phaseseeker/RotorRE/pics/front_resized.jpg

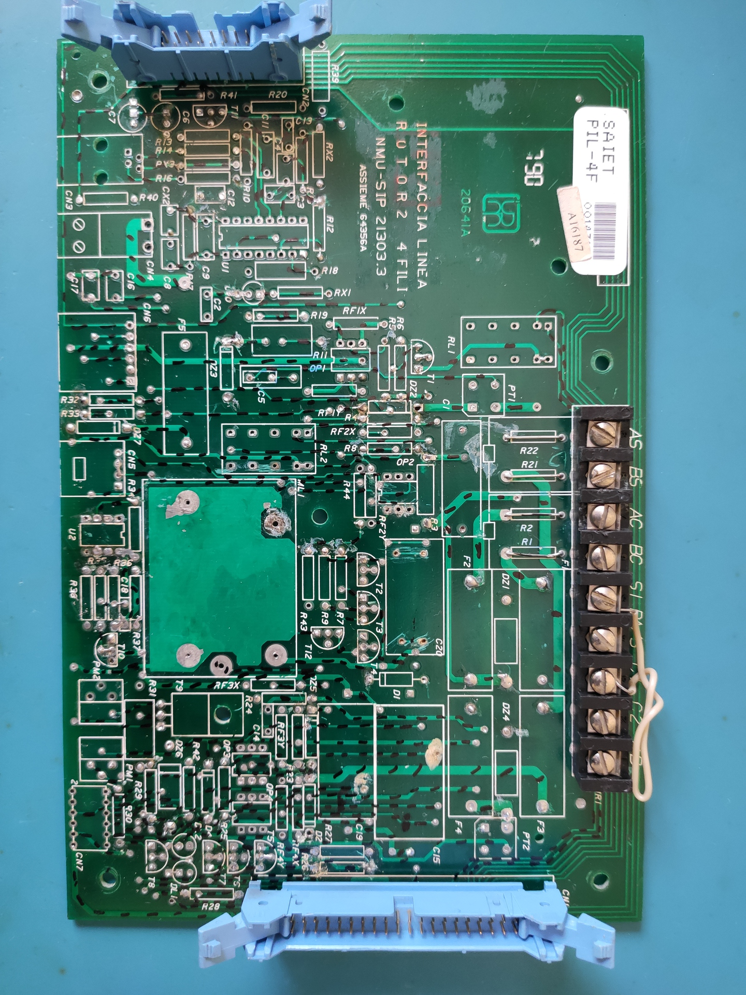
pics/front_resized.jpg
