phaseseeker/RotorRE/pics/IMG_20210405_110229_resized.jpg

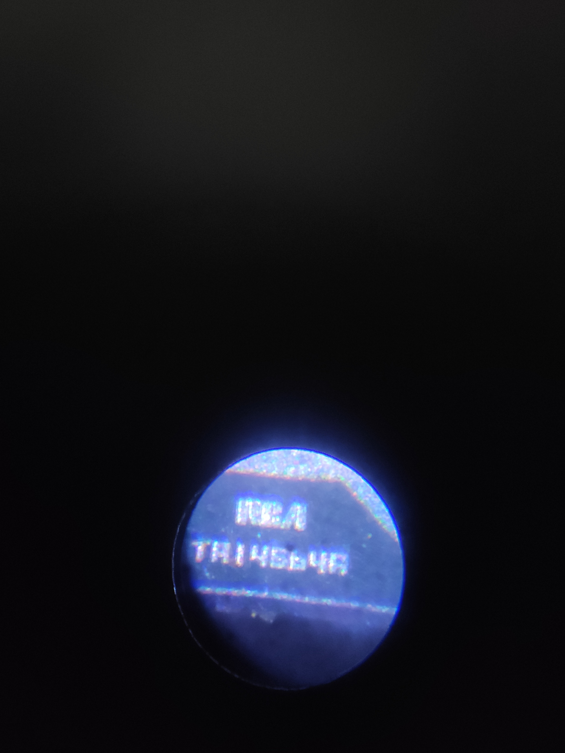
pics/IMG_20210405_110229_resized.jpg
