phaseseeker/RotorRE/pics/IMG_20210417_101937_resized.jpg

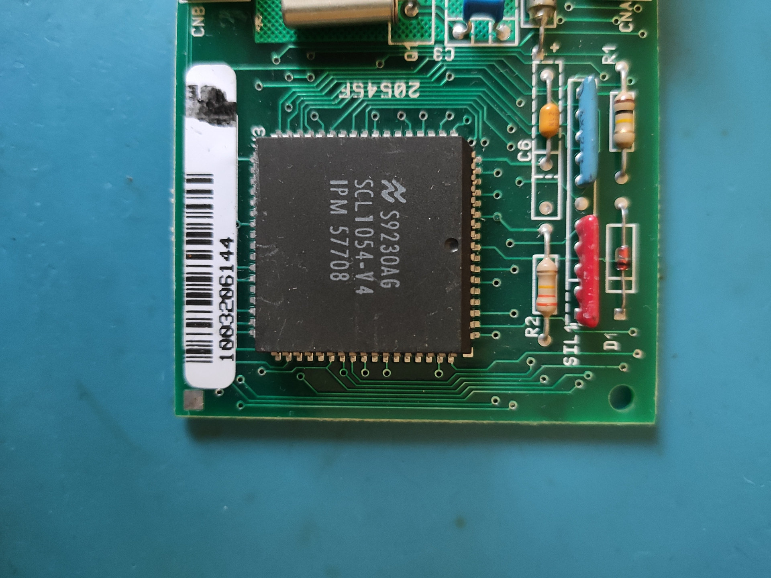
pics/IMG_20210417_101937_resized.jpg
