phaseseeker/RotorRE/pics/IMG_20210930_120020_resized.jpg

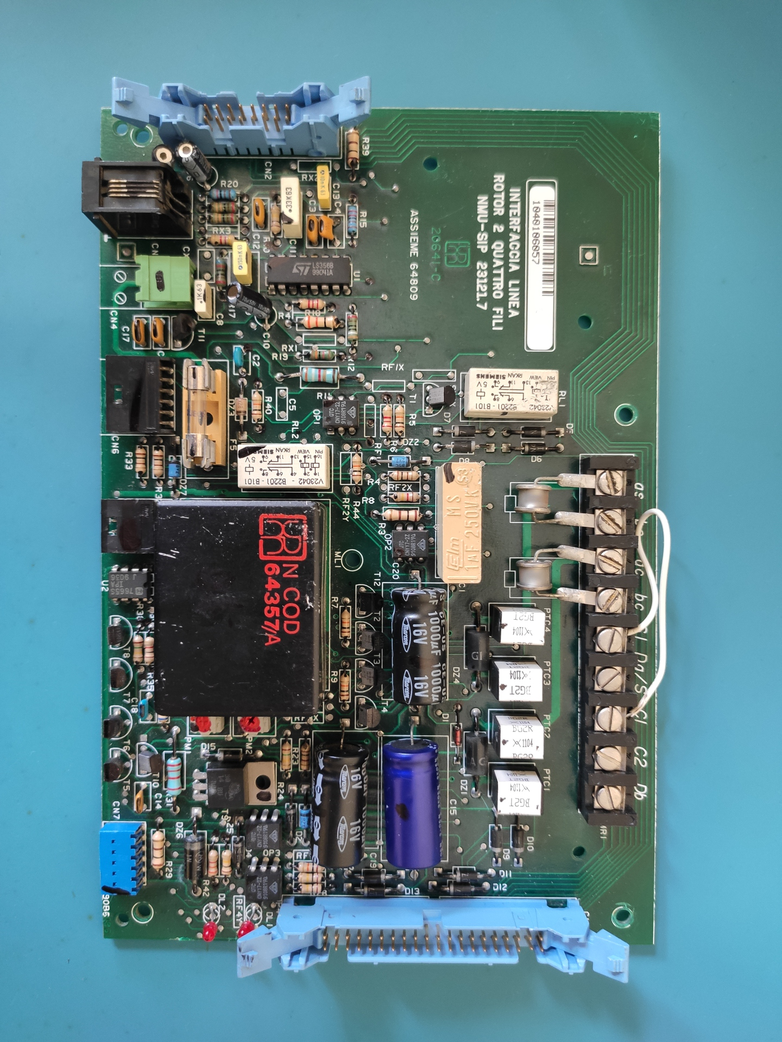
pics/IMG_20210930_120020_resized.jpg
