phaseseeker/RotorRE/pics/IMG_20210930_120023_resized.jpg

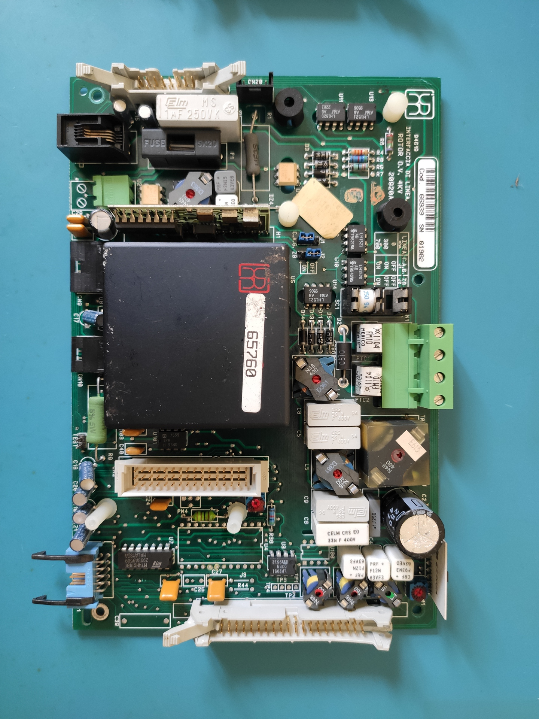
pics/IMG_20210930_120023_resized.jpg
