phaseseeker/RotorRE/pics/IMG_20210930_120042_resized.jpg

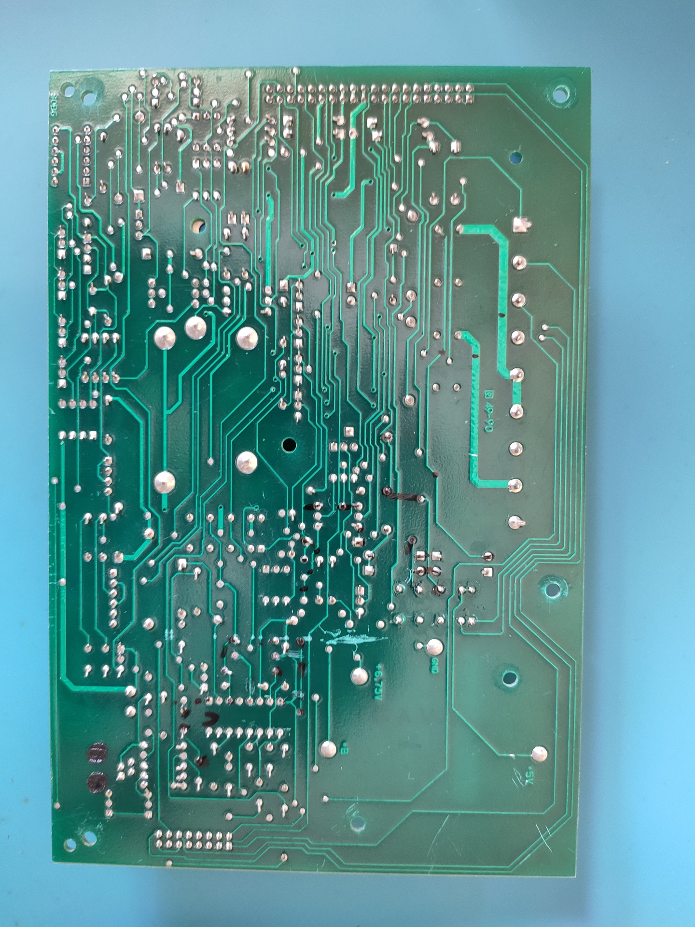
pics/IMG_20210930_120042_resized.jpg
