phaseseeker/RotorRE/pics/IMG_20210930_120044_resized.jpg

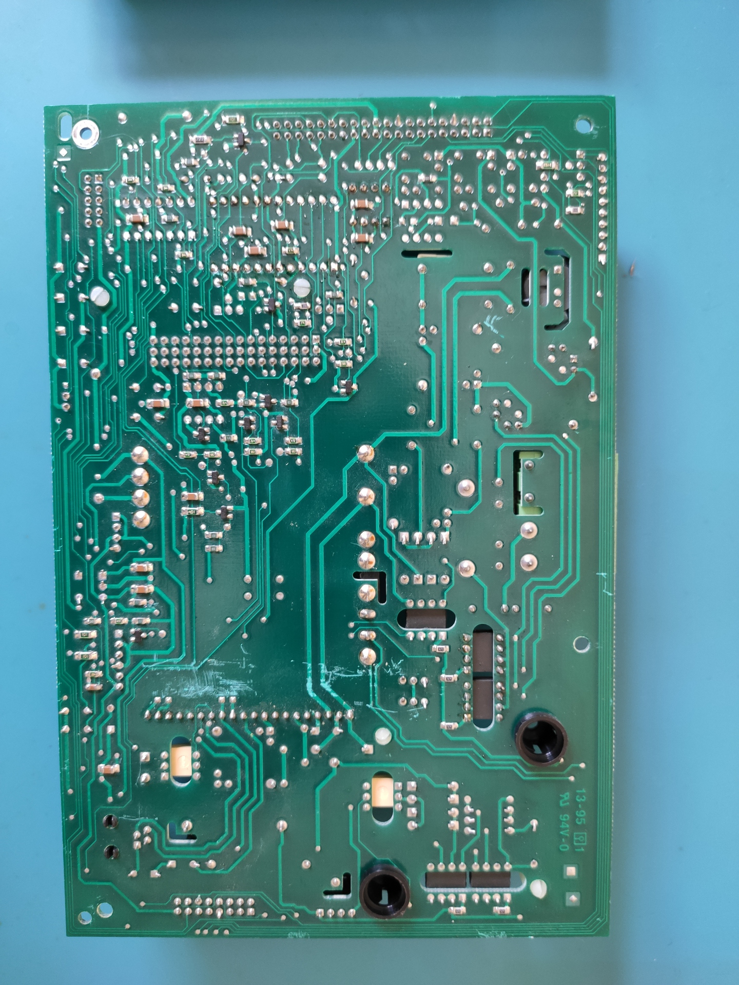
pics/IMG_20210930_120044_resized.jpg
