phaseseeker/RotorRE/pics/IMG_20210930_120053_resized.jpg

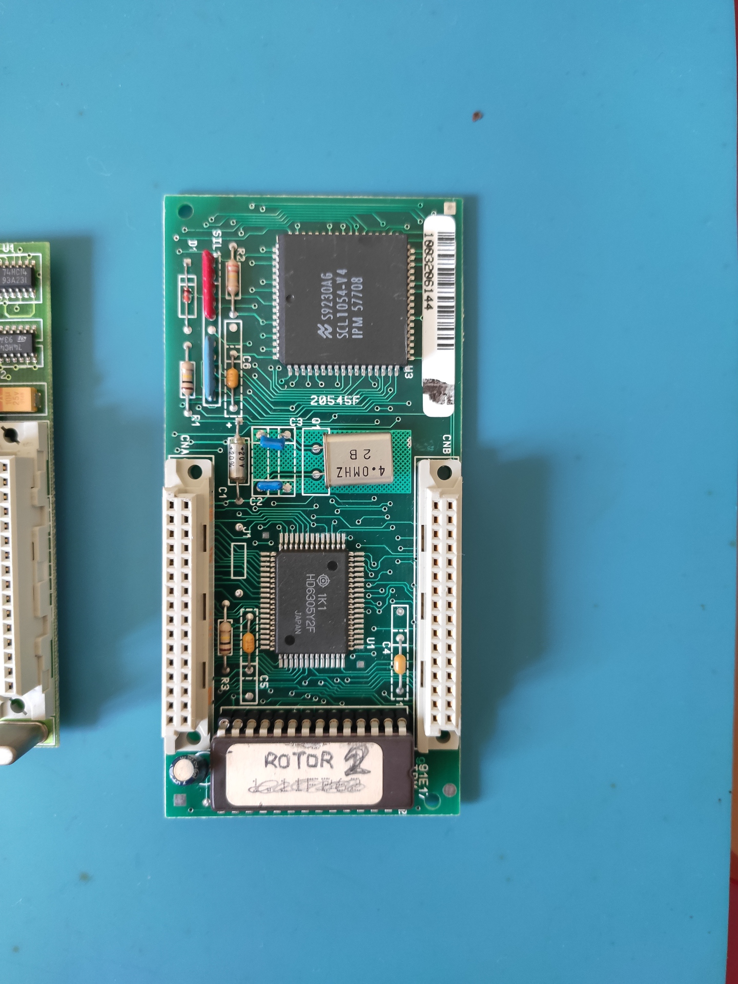
pics/IMG_20210930_120053_resized.jpg
