phaseseeker/RotorRE/pics/IMG_20210930_120104_resized.jpg

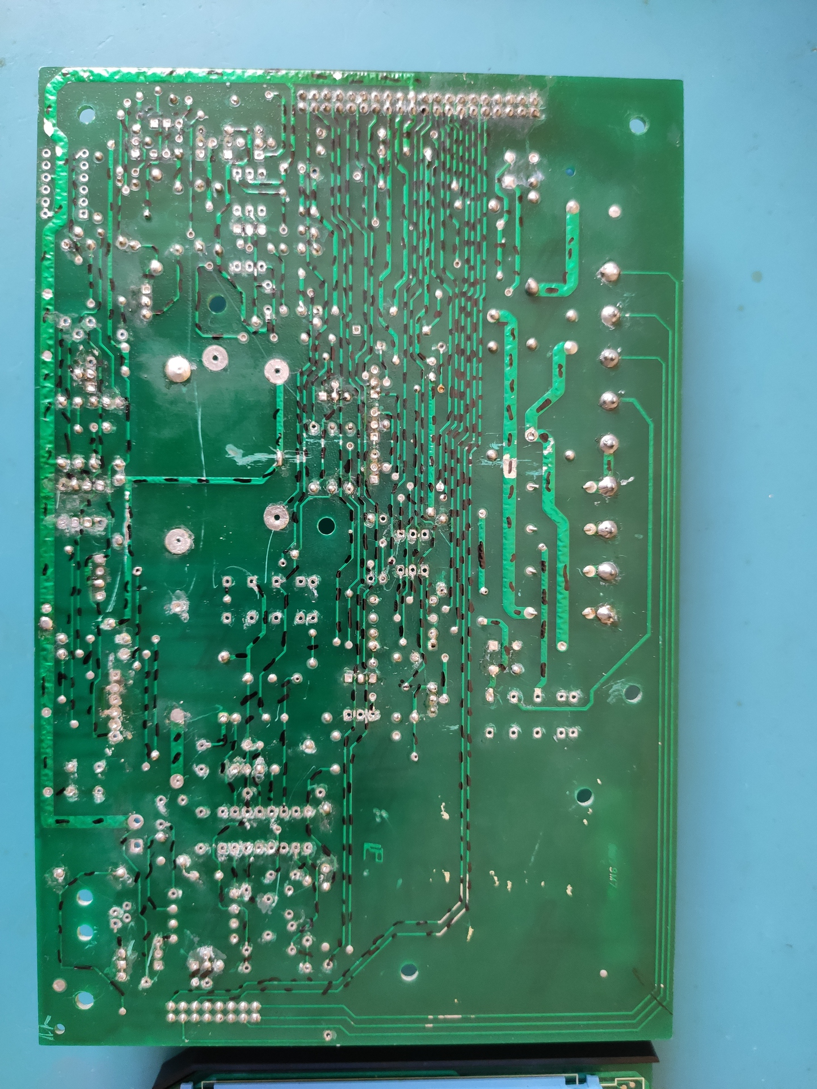
pics/IMG_20210930_120104_resized.jpg
