phaseseeker/RotorRE/pics/IMG_20210930_120108_resized.jpg

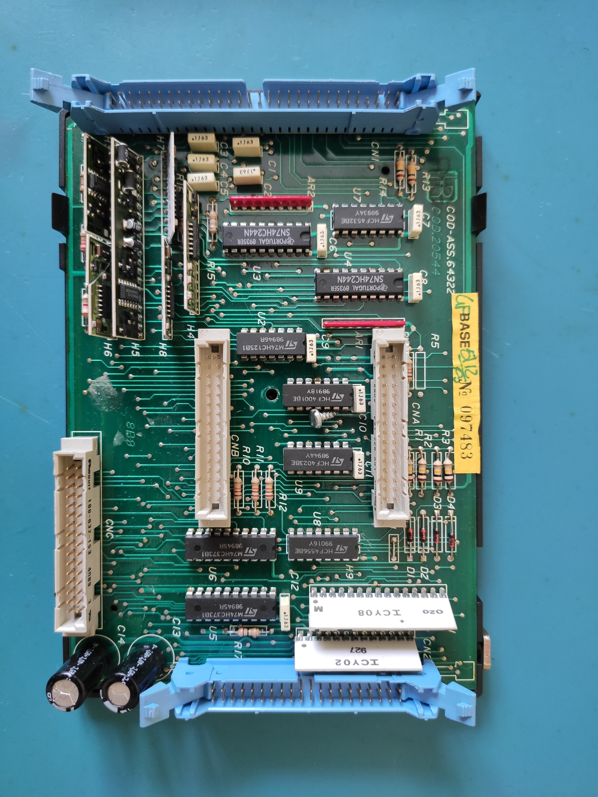
pics/IMG_20210930_120108_resized.jpg
