phaseseeker/RotorRE/pics/IMG_20210930_120112_resized.jpg

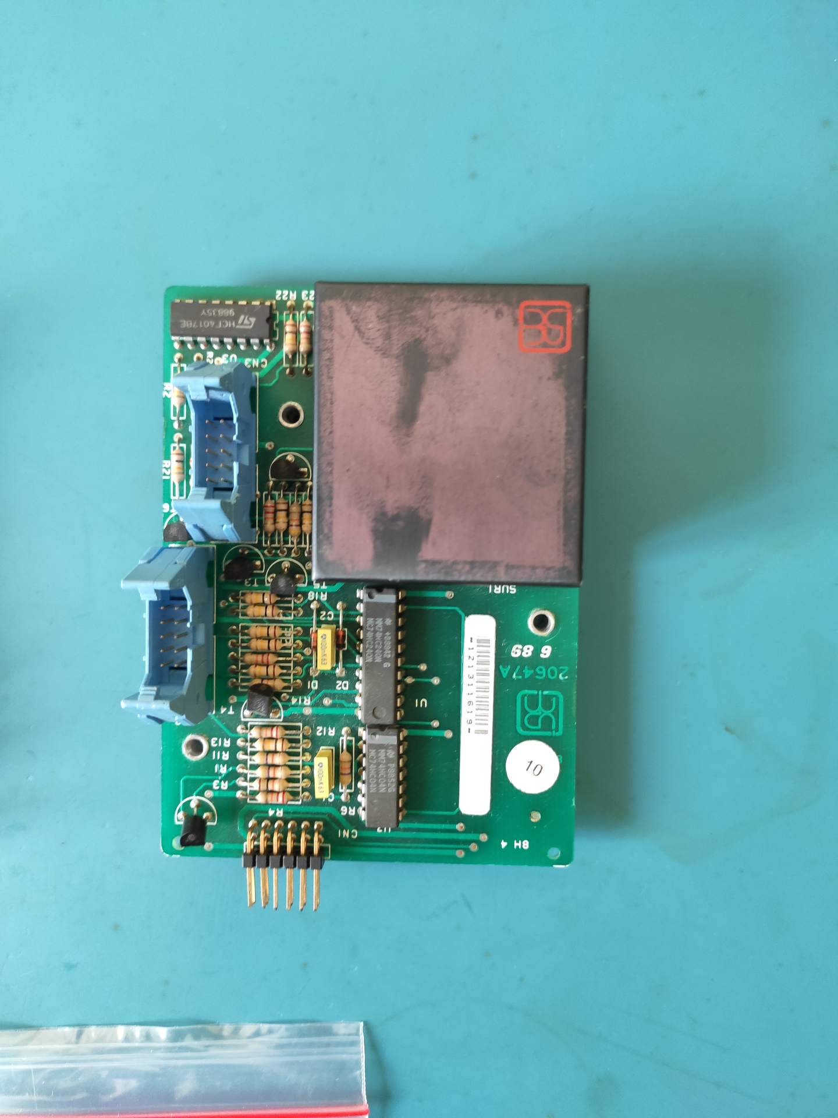
pics/IMG_20210930_120112_resized.jpg
