phaseseeker/RotorRE/pics/IMG_20210930_120115_resized.jpg

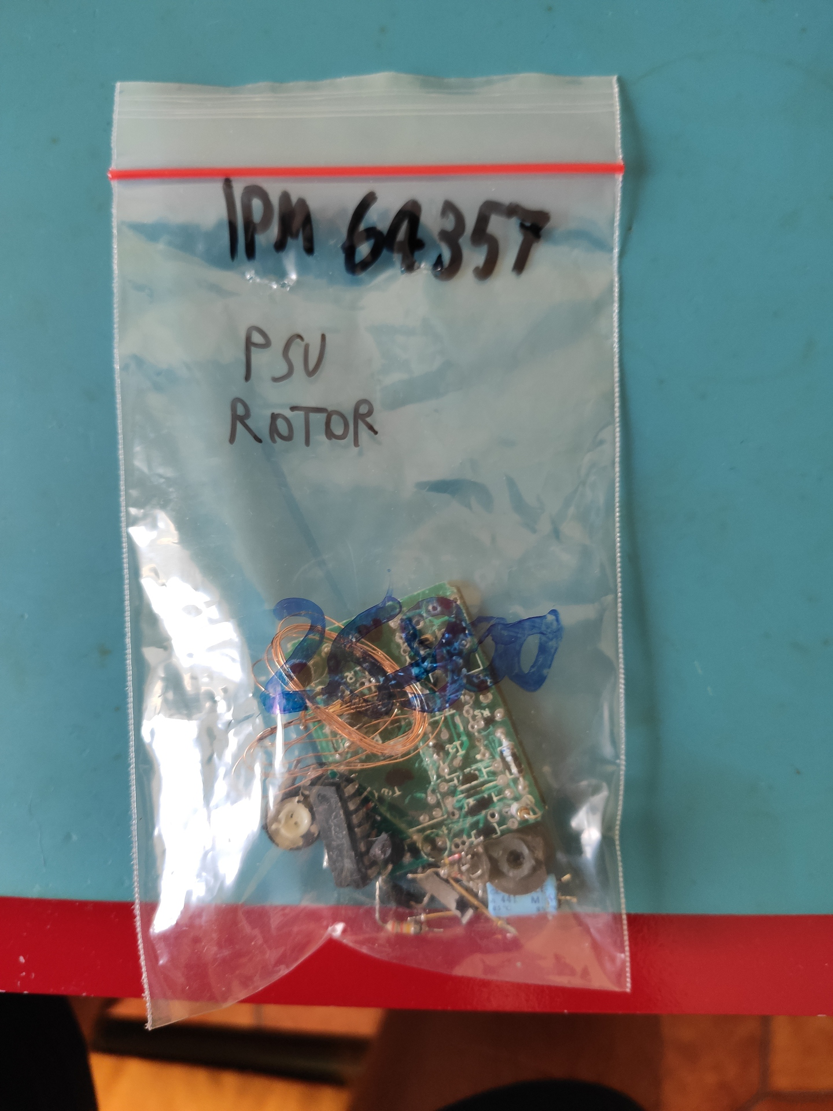
pics/IMG_20210930_120115_resized.jpg
