phaseseeker/RotorRE/pics/IMG_20210930_120138_resized.jpg

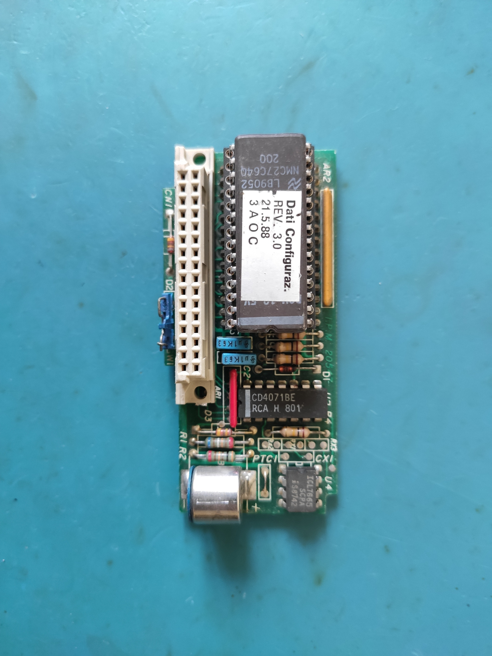
pics/IMG_20210930_120138_resized.jpg
