phaseseeker/RotorRE/pics/IMG_20210930_120150_resized.jpg

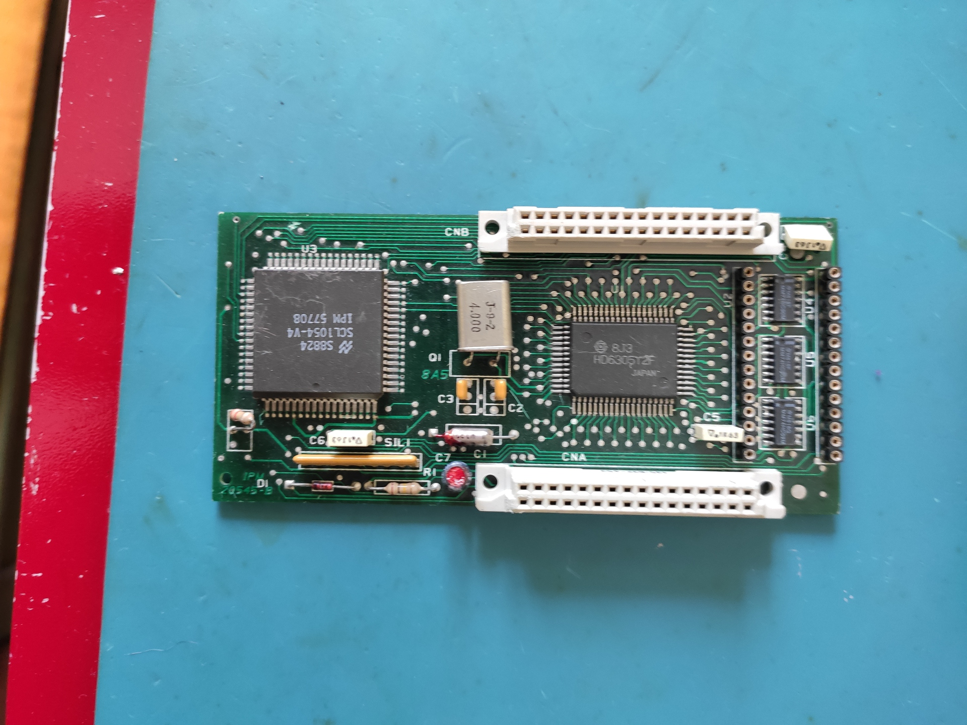
pics/IMG_20210930_120150_resized.jpg
