phaseseeker/RotorRE/pics/IMG_20210930_120319_resized.jpg

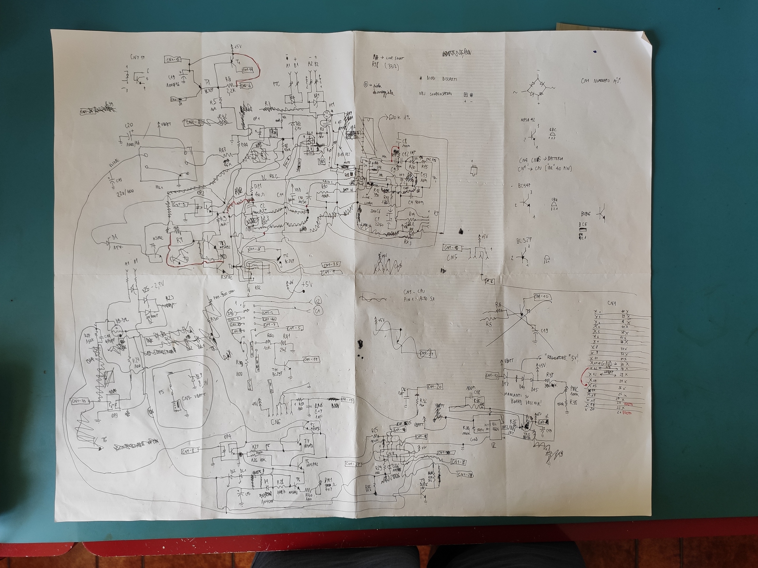
pics/IMG_20210930_120319_resized.jpg
