phaseseeker/RotorRE/pics/IMG_20210930_120355_resized.jpg

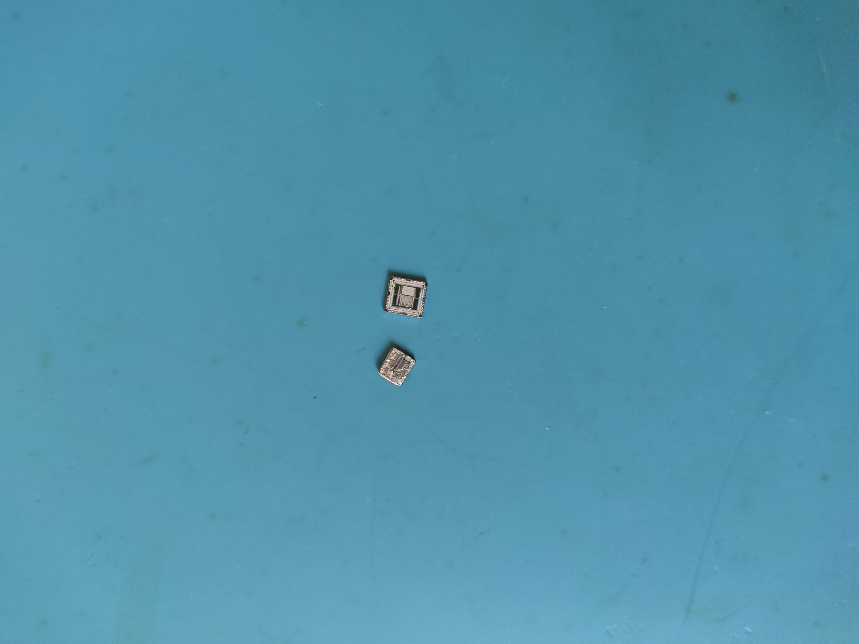
pics/IMG_20210930_120355_resized.jpg
