phaseseeker/RotorRE/pics/IMG_20210930_120400_resized.jpg

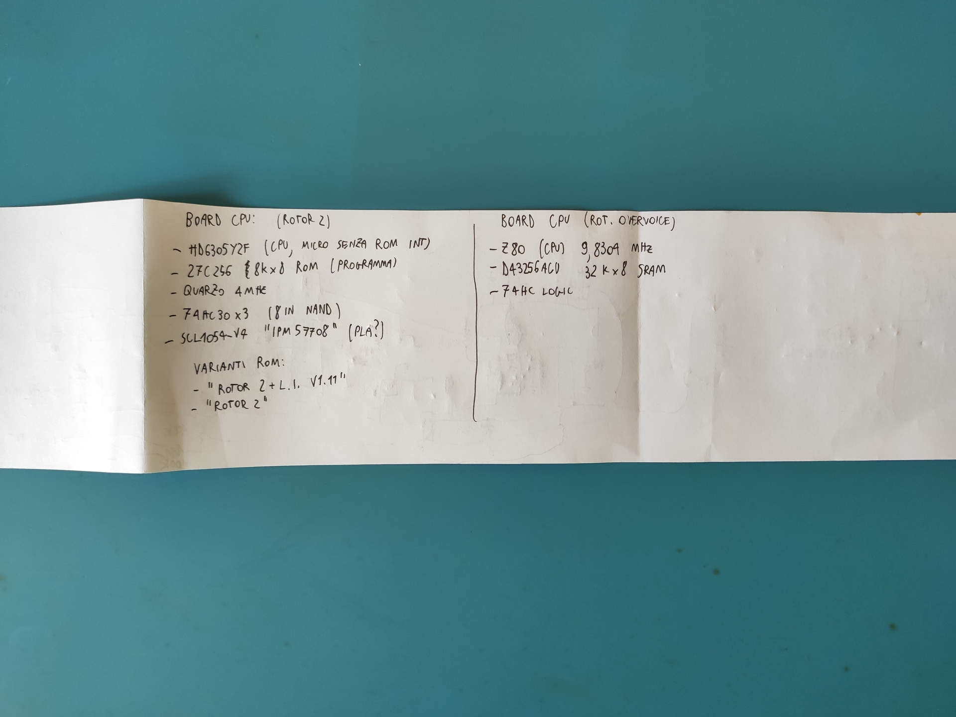
pics/IMG_20210930_120400_resized.jpg
