phaseseeker/RotorRE/pics/IMG_20210930_120421_resized.jpg

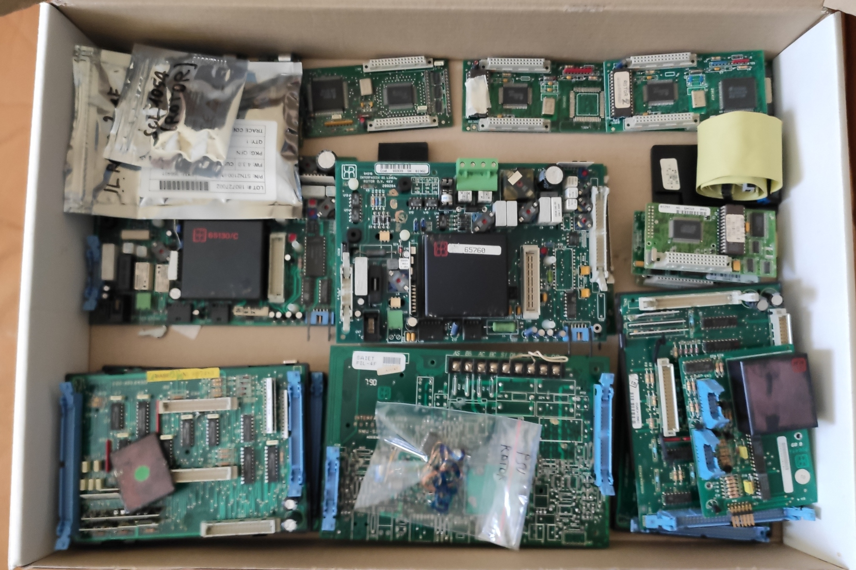
pics/IMG_20210930_120421_resized.jpg
