phaseseeker/RotorRE/pics/IMG_20210930_120958_resized.jpg

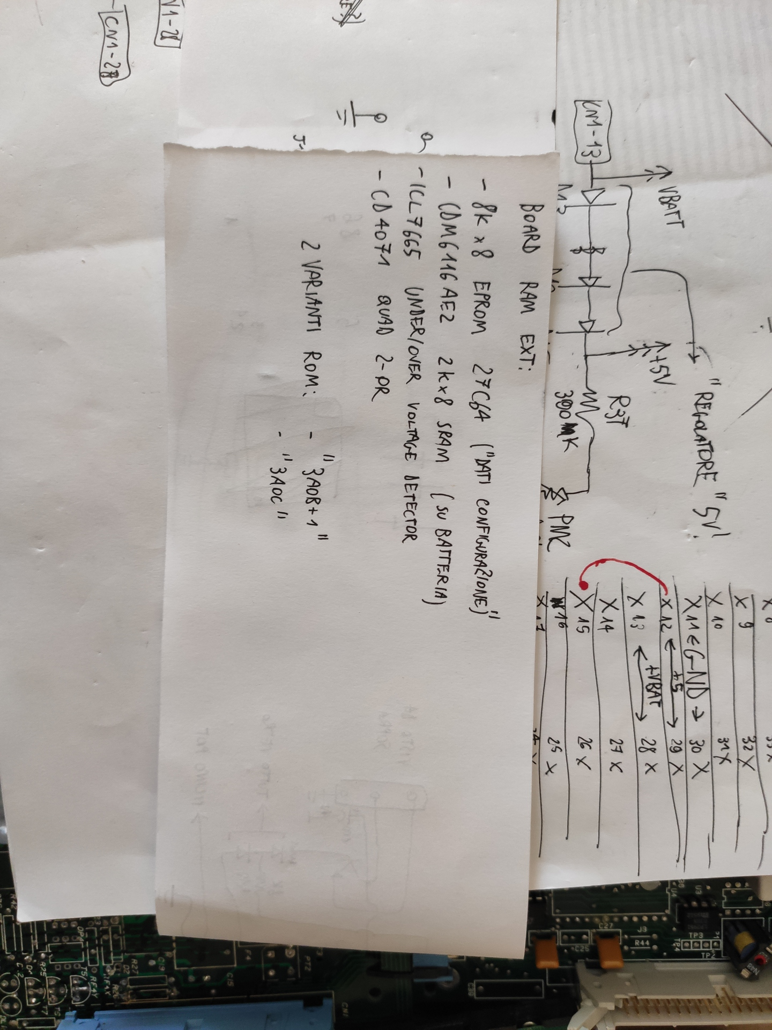
pics/IMG_20210930_120958_resized.jpg
