phaseseeker/RotorRE/pics/internals_Mech.jpg

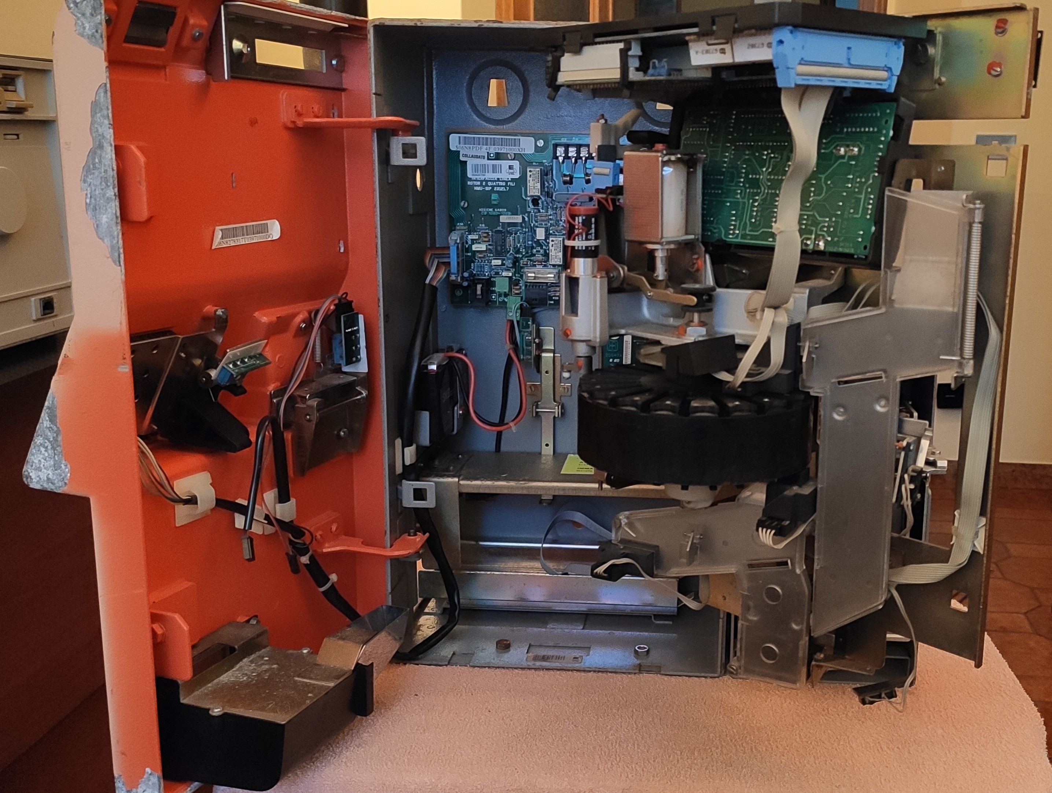
pics/internals_Mech.jpg
