phaseseeker/RotorRE/pics/internals_noMech.jpg

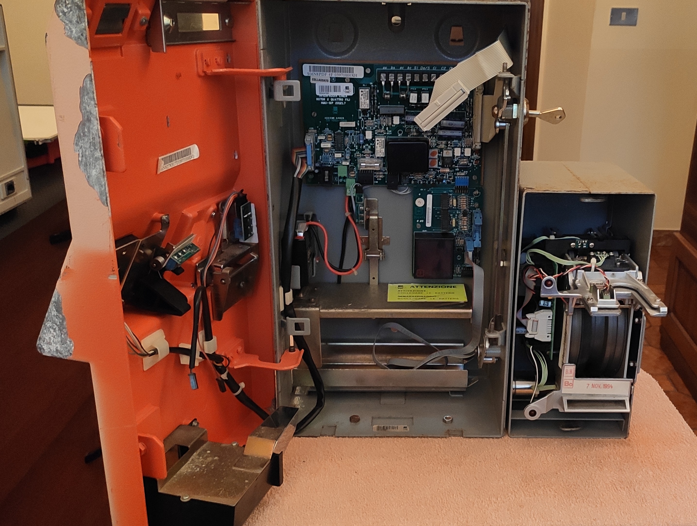
pics/internals_noMech.jpg
