phaseseeker/RotorRE/pics/liod_0_resized.jpg

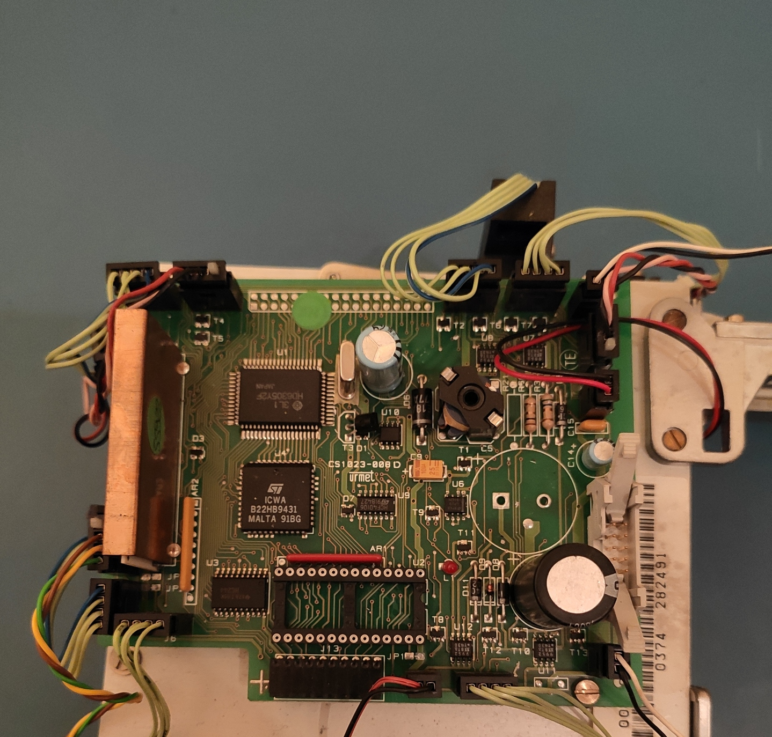
pics/liod_0_resized.jpg
