phaseseeker/RotorRE/pics/liod_1_resized.jpg

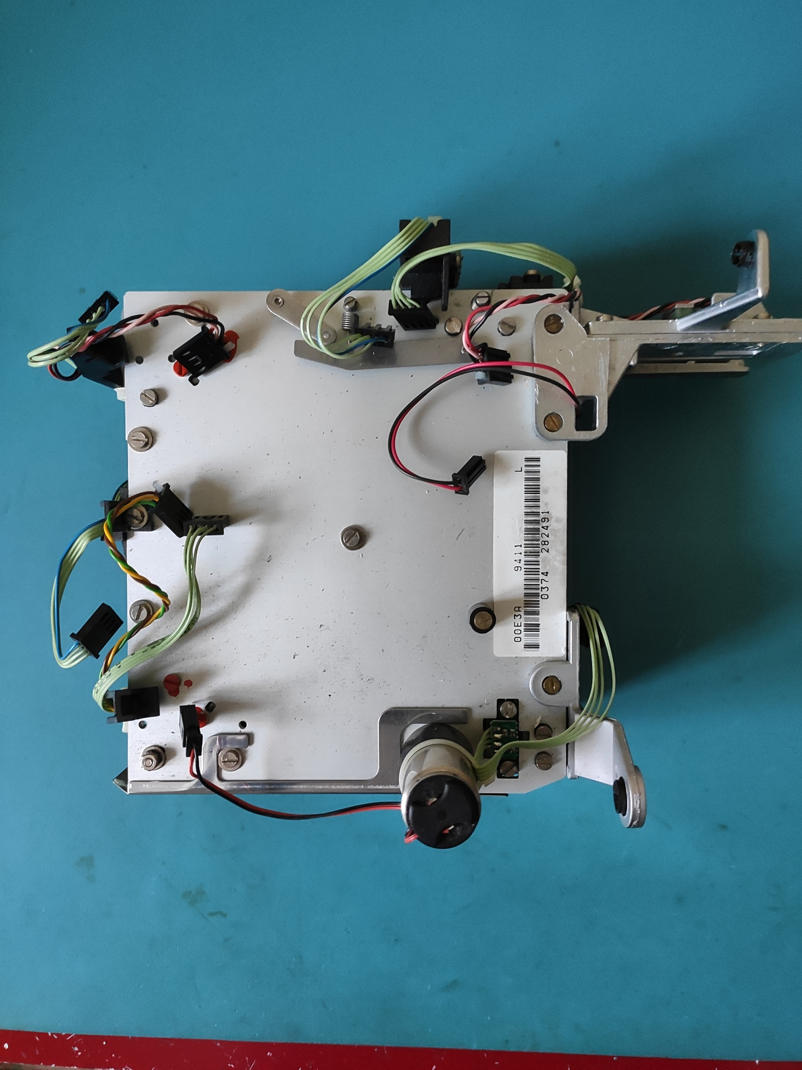
pics/liod_1_resized.jpg
