phaseseeker/RotorRE/pics/liod_2_resized.jpg

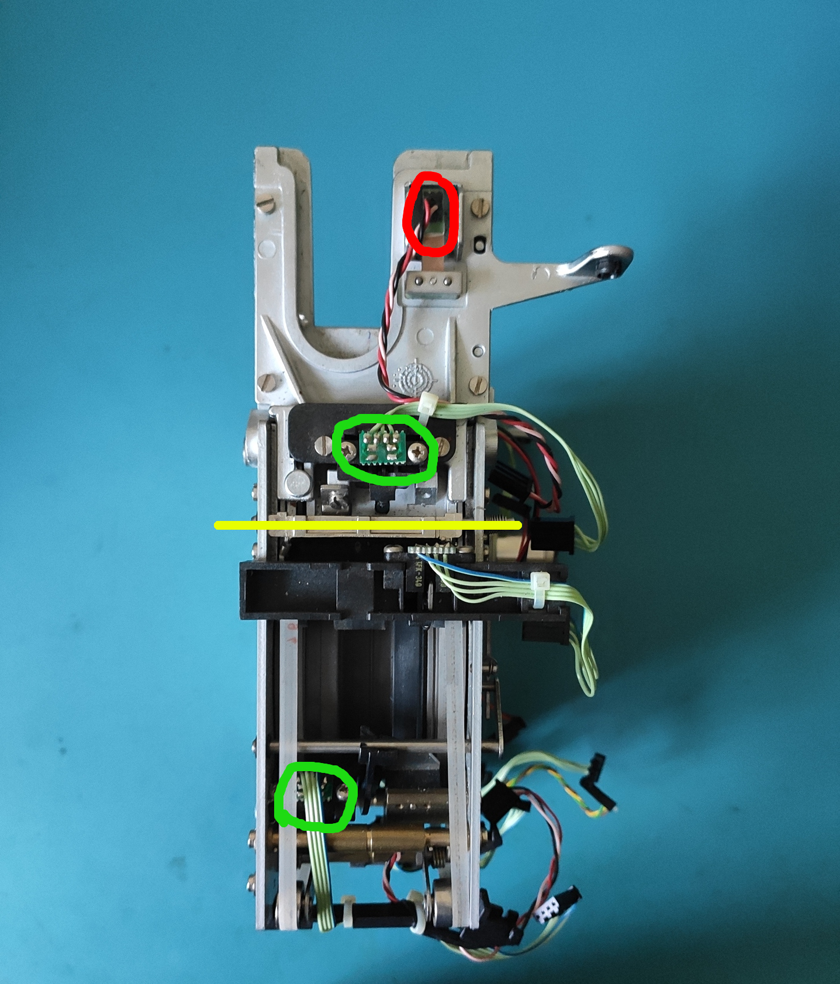
pics/liod_2_resized.jpg
