phaseseeker/RotorRE/pics/liod_3_resized.jpg

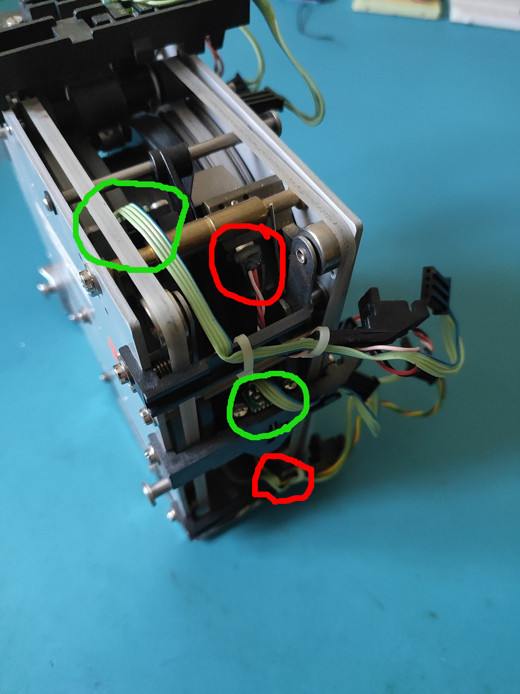
pics/liod_3_resized.jpg
