phaseseeker/RotorRE/pics/liod_4_resized.jpg

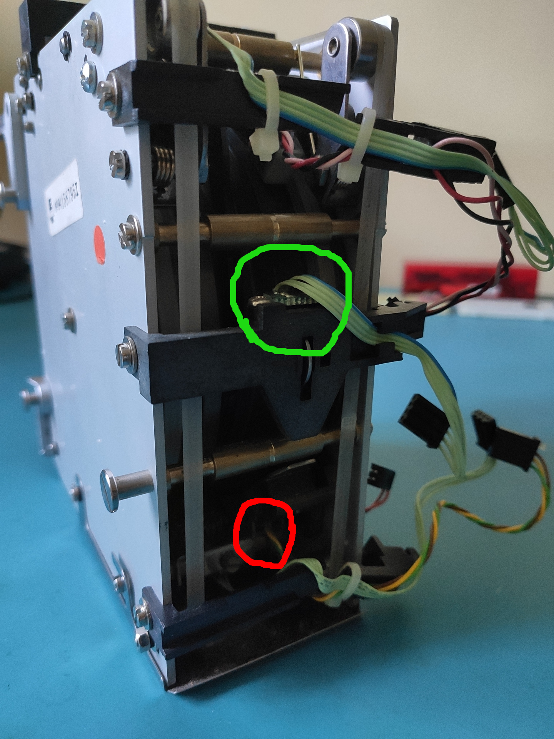
pics/liod_4_resized.jpg
