phaseseeker/RotorRE/pics/liod_5_resized.jpg

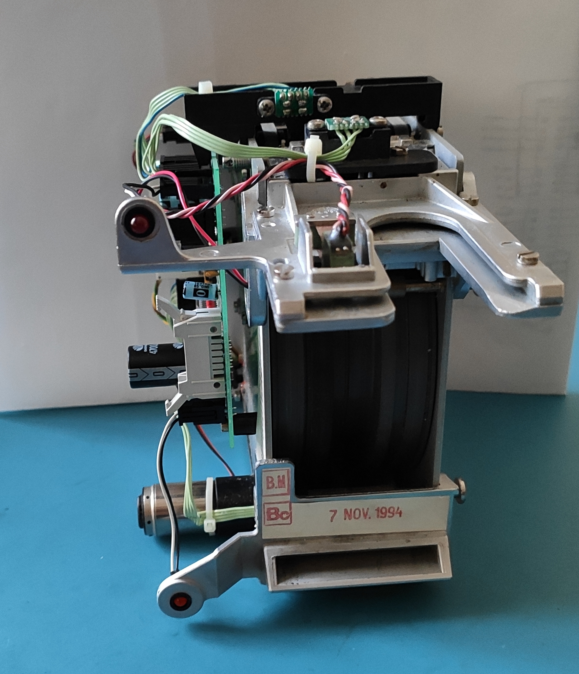
pics/liod_5_resized.jpg
