phaseseeker/RotorRE/pics/main_flippedup.jpg

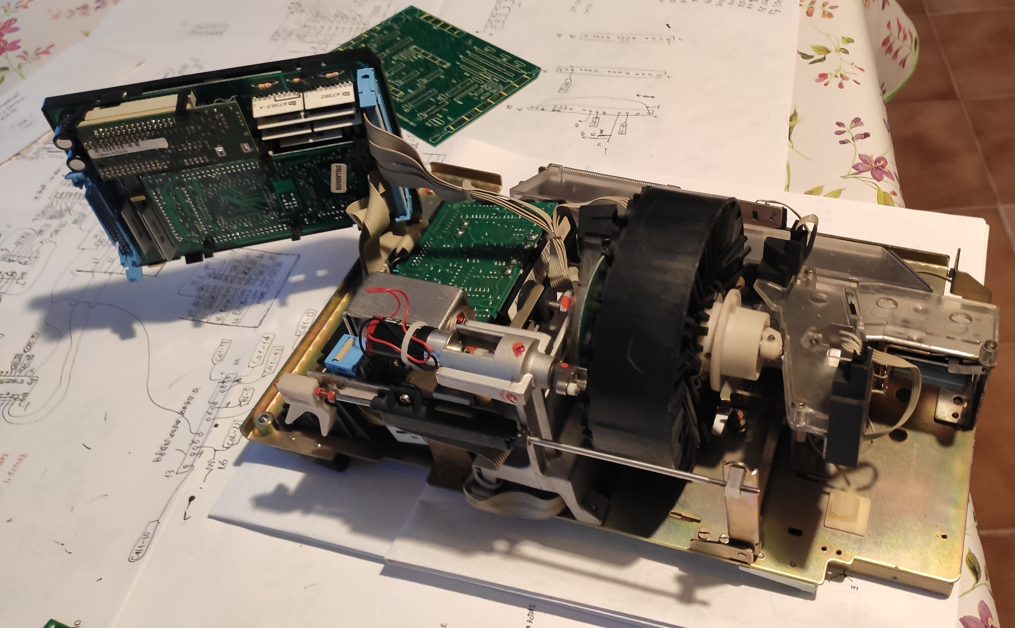
pics/main_flippedup.jpg
