phaseseeker/RotorRE/pics/main_resized.jpg

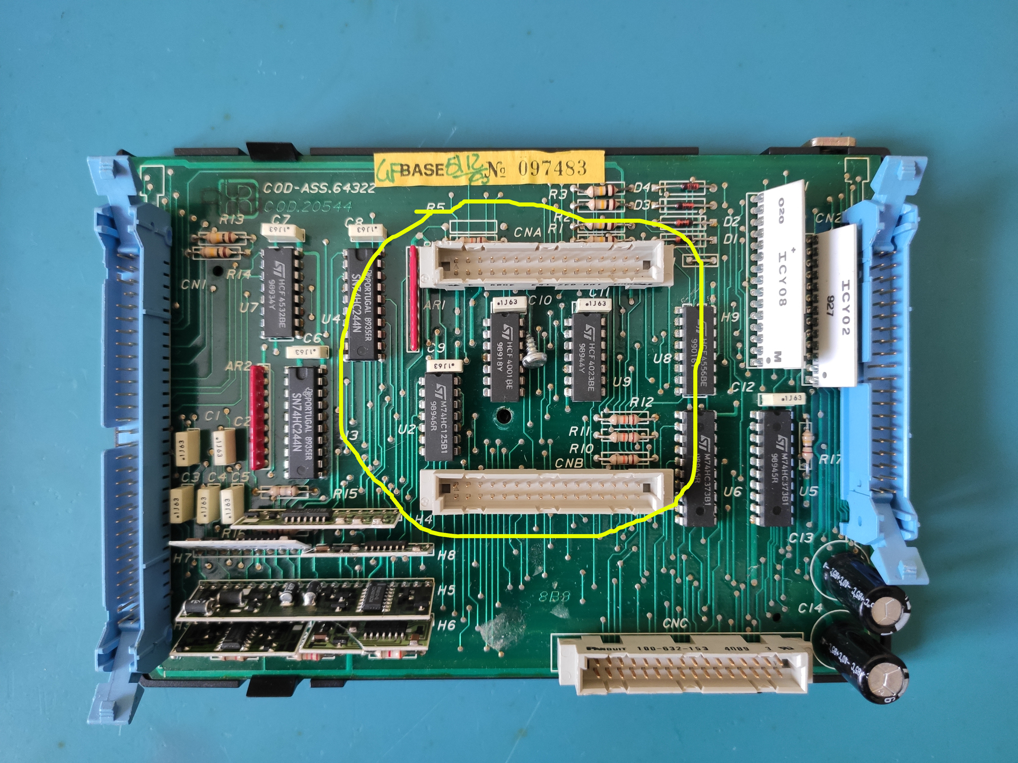
pics/main_resized.jpg
