phaseseeker/RotorRE/pics/OV_resized.jpg

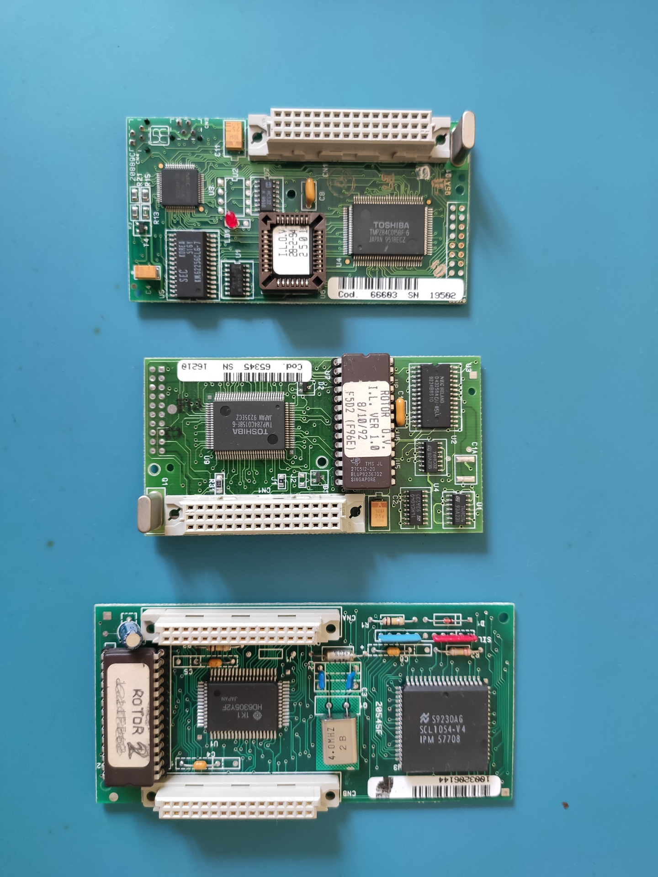
pics/OV_resized.jpg
