phaseseeker/RotorRE/pics/phone.jpeg

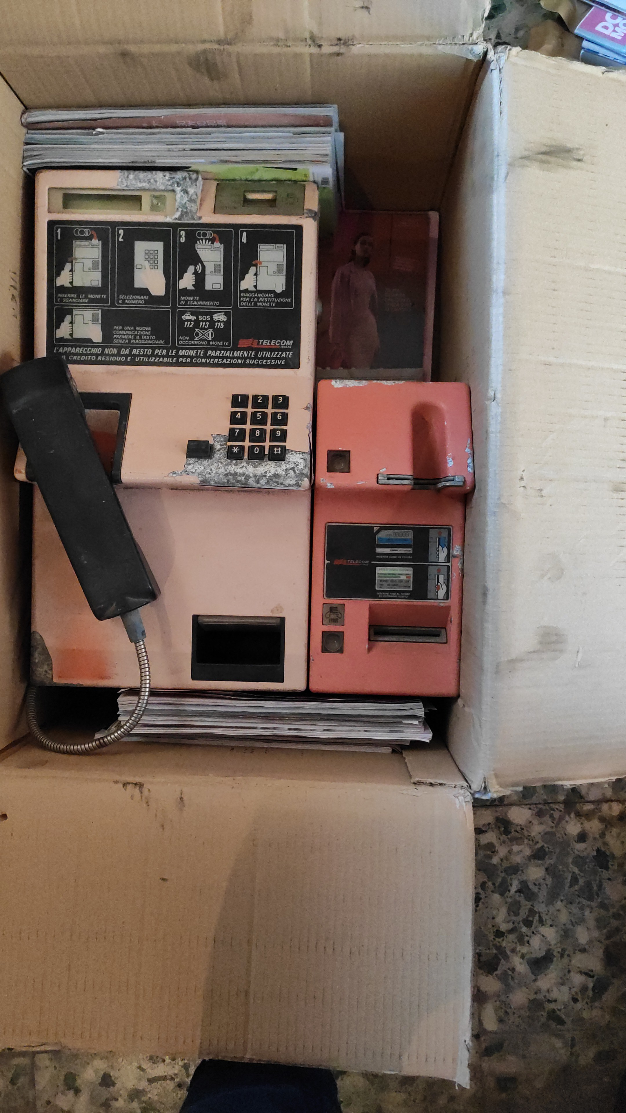
pics/phone.jpeg
