phaseseeker/RotorRE/manual/Rotor01.jpg

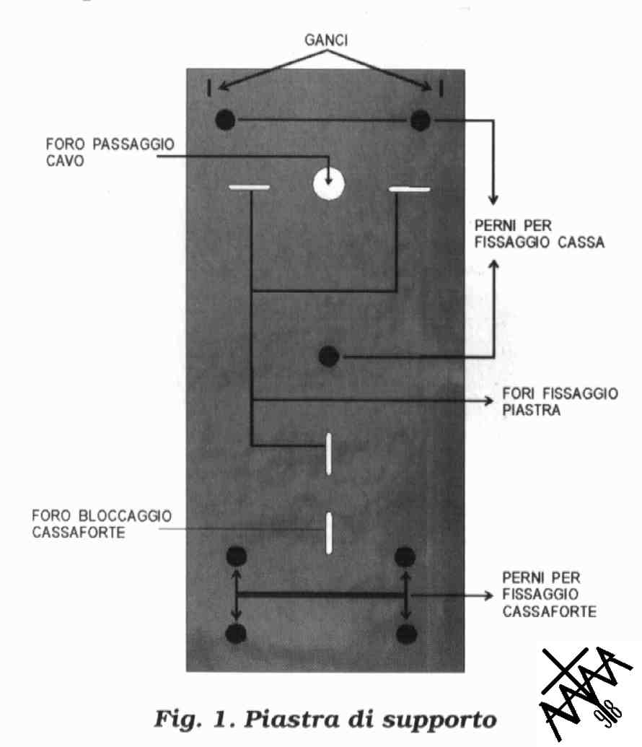
manual/Rotor01.jpg
