phaseseeker/RotorRE/manual/Rotor04.jpg

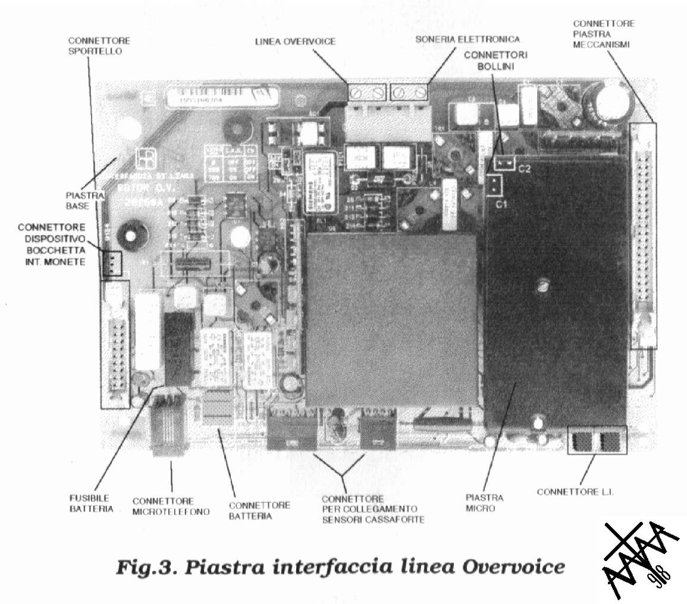
manual/Rotor04.jpg
