phaseseeker/RotorRE/manual/Rotor05.jpg

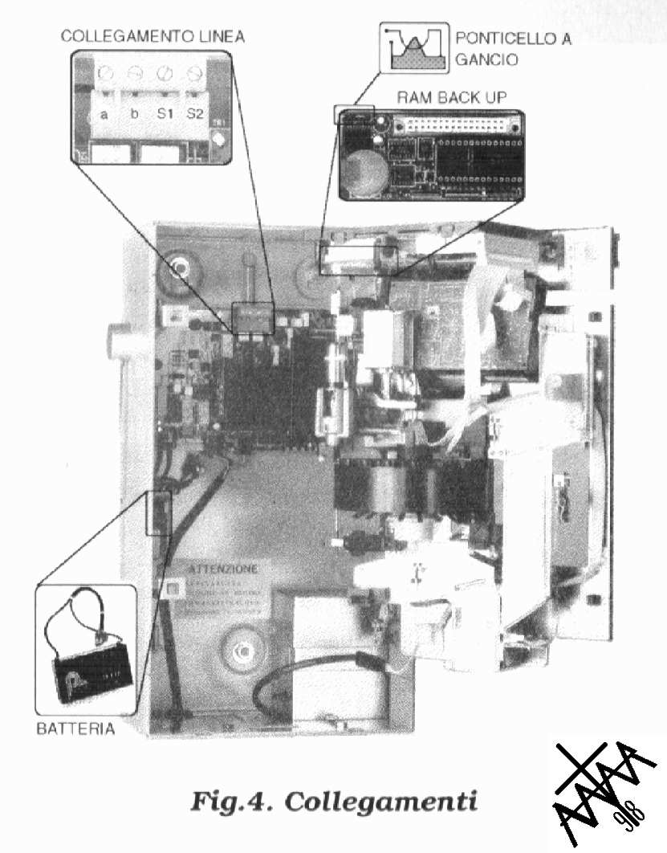
manual/Rotor05.jpg
