phaseseeker/RotorRE/manual/Rotor06.jpg

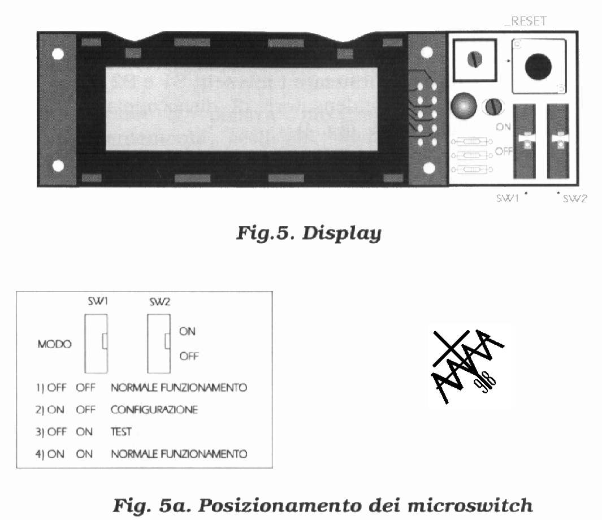
manual/Rotor06.jpg
