phaseseeker/RotorRE/manual/s-l1600 (1).png

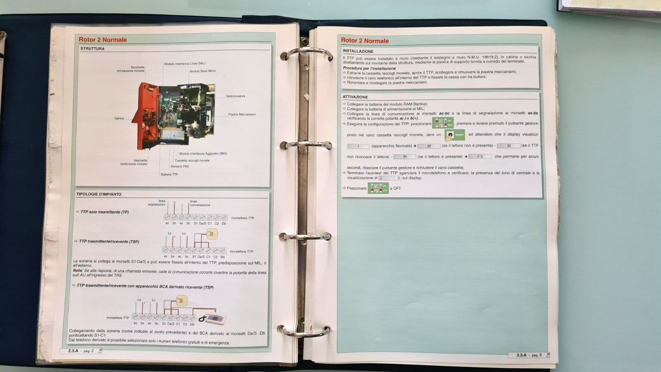
manual/s-l1600 (1).png
