phaseseeker/RotorRE/manual/s-l1600 (3).png

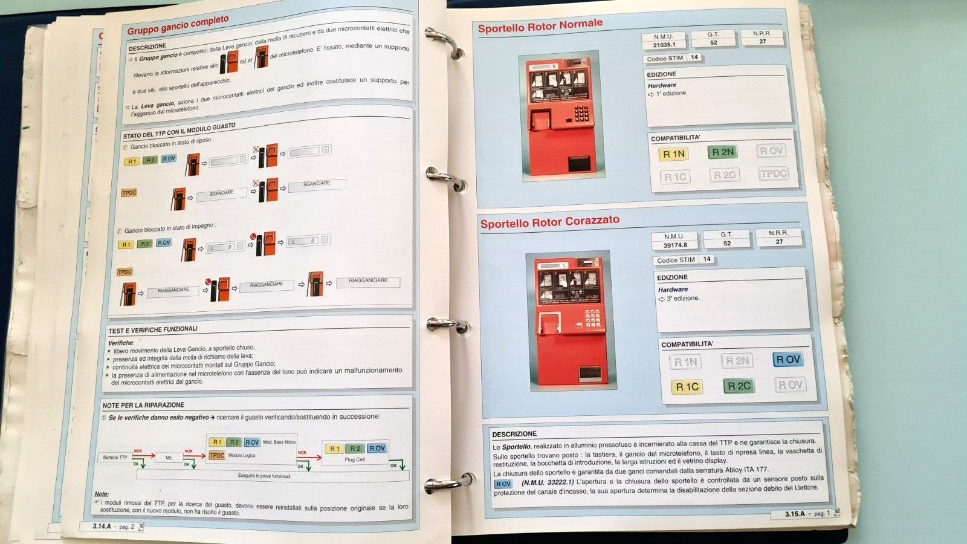
manual/s-l1600 (3).png
