phaseseeker/RotorRE/manual/s-l1600 (5).png

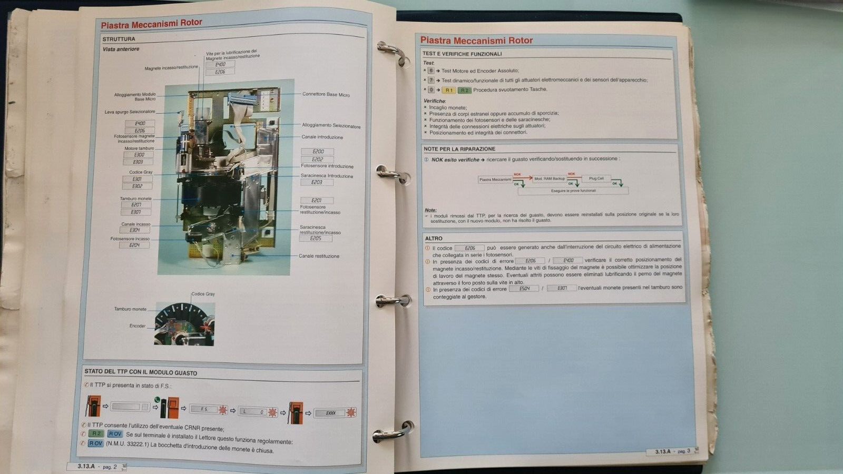
manual/s-l1600 (5).png
