phaseseeker/RotorRE/manual/s-l1600 (6).png

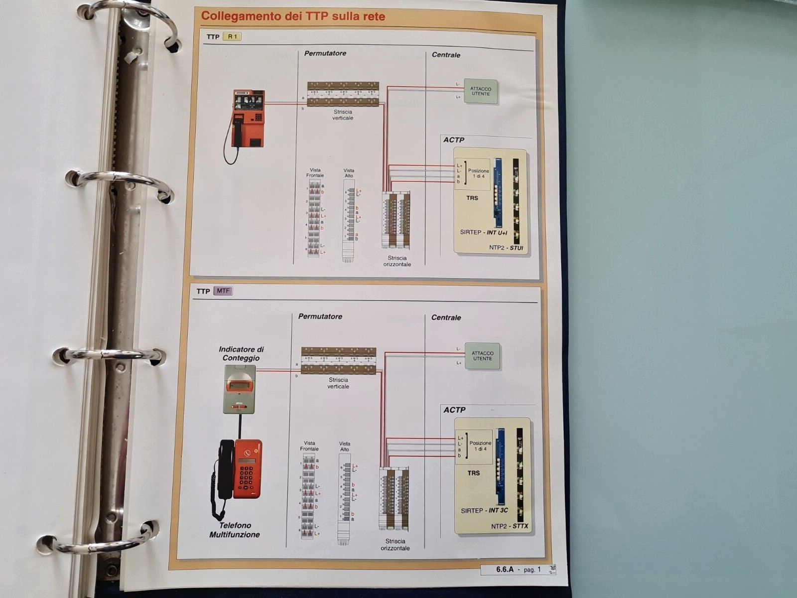
manual/s-l1600 (6).png
