phaseseeker/RotorRE/manual/s-l1600 (8).png

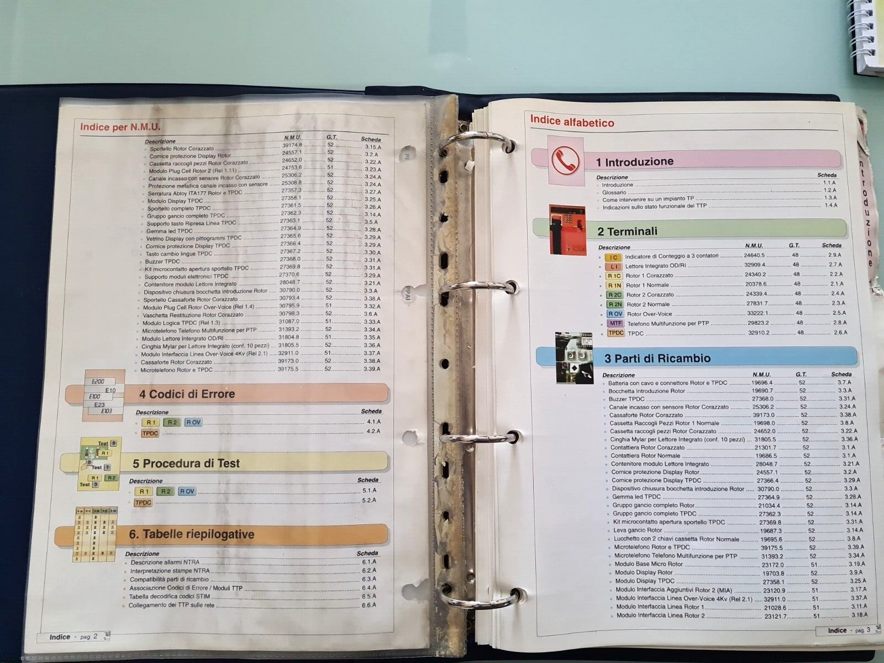
manual/s-l1600 (8).png
