phaseseeker/RotorRE/manual/s-l1600 (9).jpg

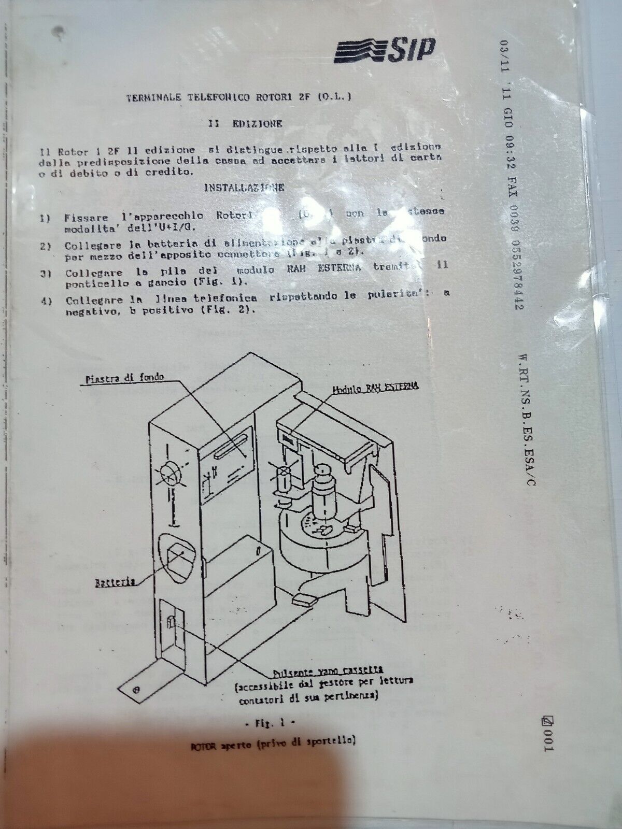
manual/s-l1600 (9).jpg
