phaseseeker/RotorRE/manual/s-l1600 (10).png

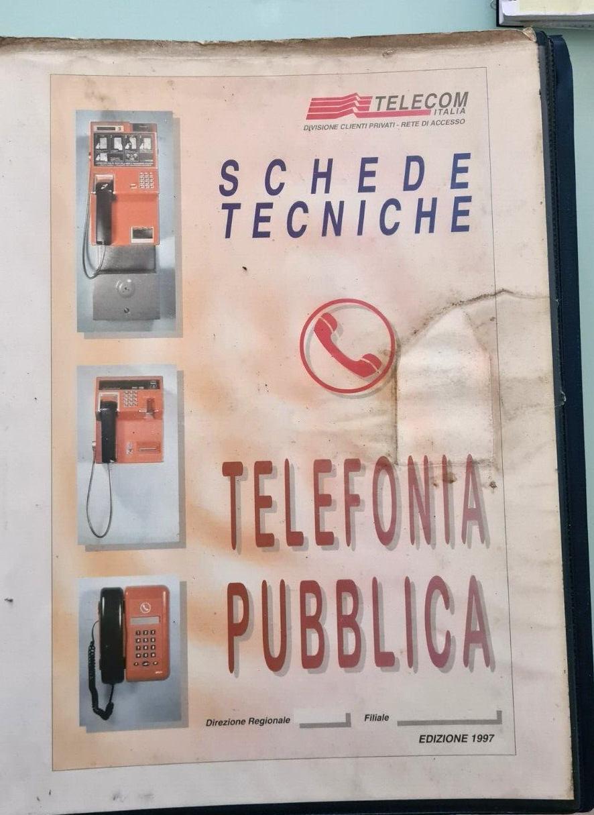
manual/s-l1600 (10).png
