phaseseeker/RotorRE/manual/s-l1600.png

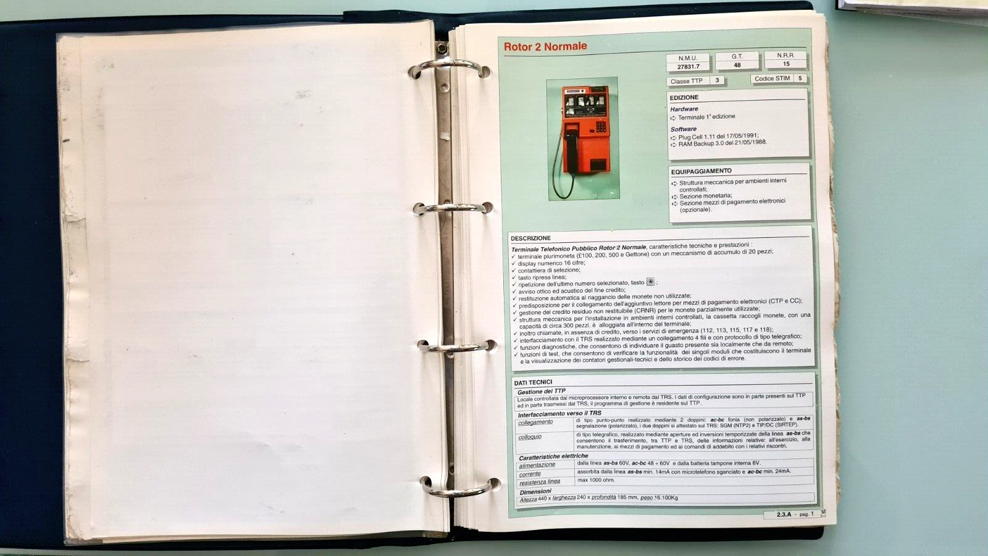
manual/s-l1600.png
