phaseseeker/RotorRE/schematics/RAM.sch

## EAGLE design schematics/RAM.sch (2022-10-19)

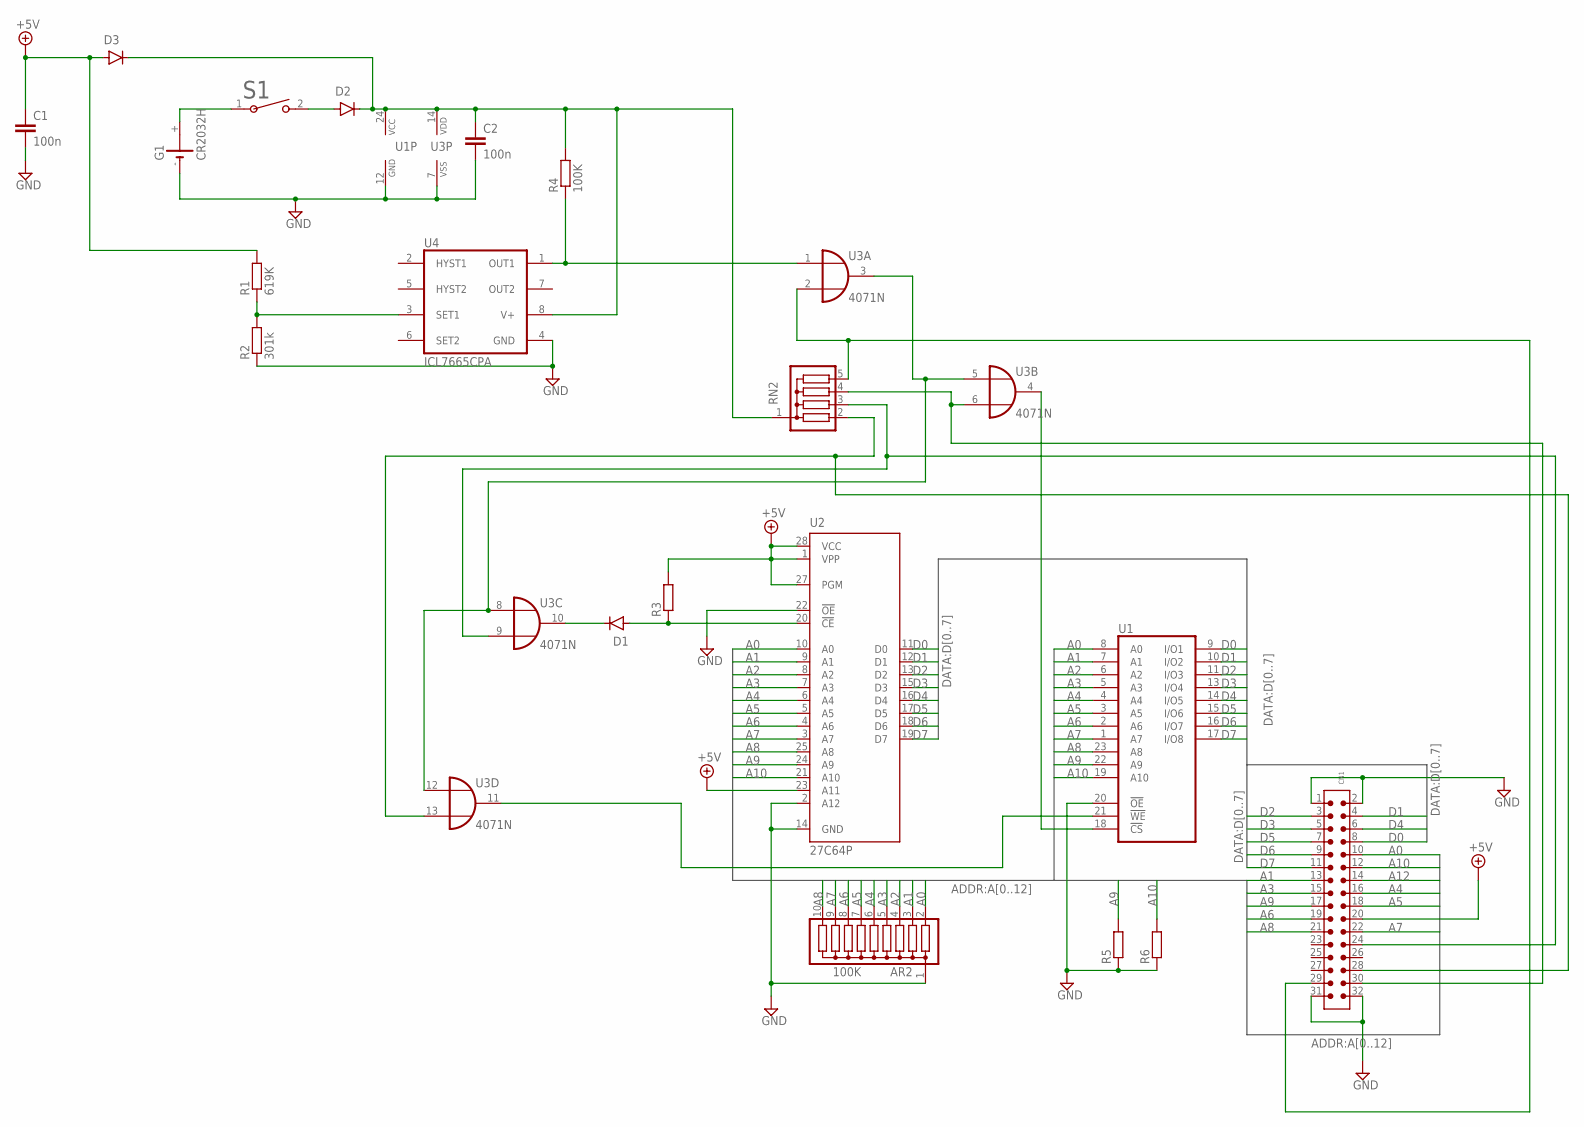
[picture p74: schematic RAM.sch]

Parts:
AR2: 100K; SIL10
C1, C2: 100n; C050-024X044
CN1: 6130XX21121_61303221121; 61303221121
D1, D2, D3: 1N4007; DO-41
G1: CR2032H
R1: 619K; 0204/7
R2: 301k; 0204/7
R3, R5, R6: R-EU_0204/7; 0204/7
R4: 100K; 0204/7
RN2: G04R; SIL5
S1: 1825966-1; SWDIP2_256X170P100
U1: 6116P; DIL24-6
U2: 27C64P; DIL28-6
U3: 4071N; DIL14
U4: ICL7665CPA; DIL08

Connections:
+5V: C1.1, CN1.20, D3.A, R1.2, R3.2, U2.1 (VPP), U2.23 (A11), U2.27 (PGM), U2.28 (VCC)
A0: AR2.2, CN1.10, U1.8 (A0), U2.10 (A0)
A1: AR2.3, CN1.13, U1.7 (A1), U2.9 (A1)
A2: AR2.4, U1.6 (A2), U2.8 (A2)
A3: AR2.5, CN1.15, U1.5 (A3), U2.7 (A3)
A4: AR2.6, CN1.16, U1.4 (A4), U2.6 (A4)
A5: AR2.7, CN1.18, U1.3 (A5), U2.5 (A5)
A6: AR2.8, CN1.19, U1.2 (A6), U2.4 (A6)
A7: AR2.9, CN1.22, U1.1 (A7), U2.3 (A7)
A8: AR2.10, CN1.21, U1.23 (A8), U2.25 (A8)
A9: CN1.17, R5.2, U1.22 (A9), U2.24 (A9)
A10: CN1.12, R6.2, U1.19 (A10), U2.21 (A10)
A12: CN1.14
D0: CN1.8, U1.9 (I/O1), U2.11 (D0)
D1: CN1.4, U1.10 (I/O2), U2.12 (D1)
D2: CN1.3, U1.11 (I/O3), U2.13 (D2)
D3: CN1.5, U1.13 (I/O4), U2.15 (D3)
D4: CN1.6, U1.14 (I/O5), U2.16 (D4)
D5: CN1.7, U1.15 (I/O6), U2.17 (D5)
D6: CN1.9, U1.16 (I/O7), U2.18 (D6)
D7: CN1.11, U1.17 (I/O8), U2.19 (D7)
GND: AR2.1, C1.2, C2.2, CN1.1, CN1.2, CN1.31, CN1.32, G1.-, R2.1, R5.1, R6.1, U1.12 (GND), U1.20 (!OE), U2.2 (A12), U2.14 (GND), U2.22 (!OE), U3.7 (VSS), U4.4 (GND)
unnamed: G1.+, S1.1
unnamed: D2.A, S1.2
unnamed: C2.1, D2.C, D3.C, R4.2, RN2.1, U1.24 (VCC), U3.14 (VDD), U4.8 (V+)
unnamed: R1.1, R2.2, U4.3 (SET1)
unnamed: R4.1, U3.1 (I0), U4.1 (OUT1)
unnamed: D1.A, R3.1, U2.20 (!CE)
unnamed: U1.18 (!CS), U3.4 (O)
unnamed: CN1.24, RN2.3, U3.9 (I1)
unnamed: U3.3 (O), U3.5 (I0), U3.8 (I0), U3.12 (I0)
unnamed: CN1.28, RN2.2, U3.13 (I1)
unnamed: D1.C, U3.10 (O)
unnamed: CN1.29, RN2.5, U3.2 (I1)
unnamed: CN1.30, RN2.4, U3.6 (I1)
unnamed: U1.21 (!WE), U3.11 (O)
