phaseseeker/RotorRE/schematics/RotorPSU.sch

## EAGLE design schematics/RotorPSU.sch (2022-10-19)

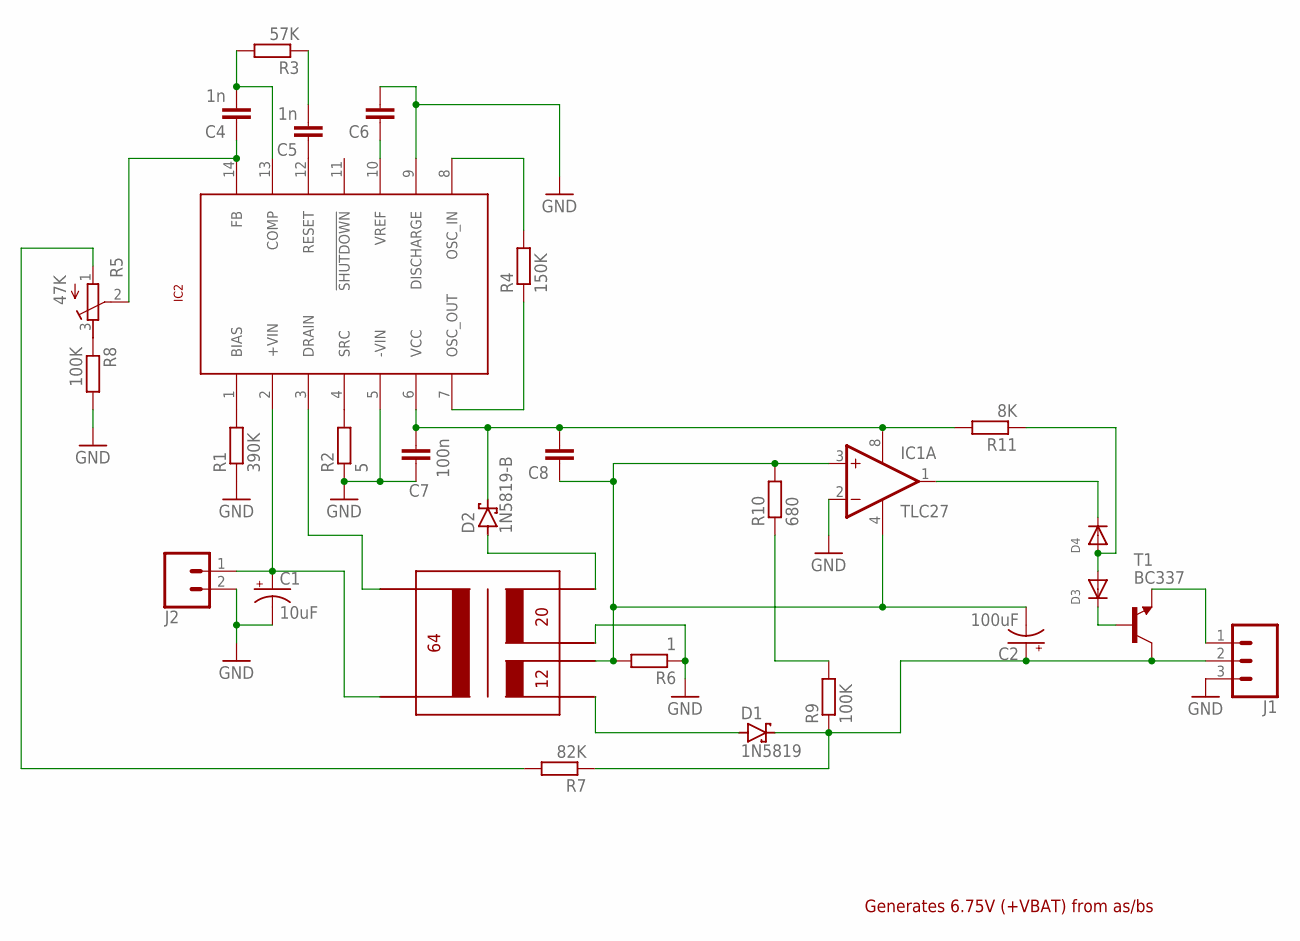
[picture p75: schematic RotorPSU.sch]

Parts:
C1: 10uF; CPOL-RADIAL-2.5MM-5MM
C2: 100uF; CPOL-RADIAL-2.5MM-6.5MM
C4, C5: 1n; C025-025X050
C6, C8: C-EU025-025X050; C025-025X050
C7: 100n; C025-025X050
D1: 1N5819; DO41-7.6
D2: 1N5819-B; DO41-7.6
D3, D4: DIODEDO-1N4148; DO-1N4148
IC1: TLC27; DIL08
IC2: SI9100; DIL14
J1: CONN_03; 1X03
J2: CONN_02; 1X02
R1: 390K; 0207/7
R2: 5; 0207/7
R3: 57K; 0207/7
R4: 150K; 0207/7
R5: 47K; RTRIM3296W
R6: 1; 0207/7
R7: 82K; 0207/7
R8, R9: 100K; 0207/7
R10: 680; 0207/7
R11: 8K; 0207/7
T1: BC337; TO92
TR1: ROTOR_XFORMER

Connections:
GND: C1.2 (-), C6.2, C7.1, IC1.2 (-IN), IC2.5 (-VIN), IC2.9 (DISCHARGE), J1.3, J2.2, R1.1, R2.1, R6.1, R8.2, TR1.P$8 (20A)
unnamed: C4.1, IC2.14 (FB), R5.2 (S)
unnamed: C4.2, IC2.13 (COMP), R3.2
unnamed: IC2.1 (BIAS), R1.2
unnamed: C1.1 (+), IC2.2 (+VIN), J2.1, TR1.P$2 (64A)
unnamed: IC2.4 (SRC), R2.2
unnamed: C5.1, IC2.12 (RESET)
unnamed: C5.2, R3.1
unnamed: IC2.8 (OSC_IN), R4.2
unnamed: IC2.7 (OSC_OUT), R4.1
unnamed: C6.1, IC2.10 (VREF)
unnamed: IC2.3 (DRAIN), TR1.P$4 (64B)
unnamed: C7.2, C8.2, D2.C, IC1.8 (VDD), IC2.6 (VCC), R11.2
unnamed: D2.A, TR1.P$3 (20B)
unnamed: D1.A, TR1.P$6 (12A)
unnamed: C2.1 (+), D1.C, J1.2, R7.1, R9.1, T1.3 (C)
unnamed: C2.2 (-), C8.1, IC1.3 (+IN), IC1.4 (GND), R6.2, R10.2, TR1.P$7 (12B)
unnamed: R5.3 (E), R8.1
unnamed: R5.1 (A), R7.2
unnamed: R9.2, R10.1
unnamed: J1.1, T1.1 (E)
unnamed: D3.C, T1.2 (B)
unnamed: D3.A, D4.A, R11.1
unnamed: D4.C, IC1.1 (OUT)

Notes on the sheet:
Generates 6.75V (+VBAT) from as/bs
