phaseseeker/RotorRE/schematics/Rotor_LIOD/Rotor_LIOD.kicad_sch

## KiCad design schematics/Rotor_LIOD/Rotor_LIOD.kicad_sch (2023-12-12, an earlier design)

Schematic: Rotor_LIOD.kicad_sch

Parts:
AR1: 100K; R_Array_SIP9
AR2: 22K; R_Array_SIP10
B1: LIOD_XFMR
C1: 100n
C2, C3, C4, C7, C10, C16, C18, C19, C20, C21, C22, C23, C25, C26, C27, C28, C29, C30, C31, C32: ?
C5: (no value)
C6: 4700 uF/10 V
C8: .
C9: (Tantalum)
C11, C12: 22p?
C13: 1000 uF/35 V
C14: 10 uF/100 V
C15: 1 uF
C17: Near T4
D1, D3, D7: BAS28
D5: 1N4944; D_DO-35_SOD27_P7.62mm_Horizontal
D6: 1.5KE18A; D_DO-201AE_P15.24mm_Horizontal
D8: 1N4007; D_DO-41_SOD81_P10.16mm_Horizontal
D9: 30V?
D11: SB140; D_DO-41_SOD81_P10.16mm_Horizontal
I1: Head interface
J0, J2: (no value)
J1: 2° drum photointerrupter
J1A: Second head
J3: LIOD interface
J4: Card exit photointerrupter
J5: Main motor
J6: Drum 4° photointerrupter
J6A: Third head
J7: Drum 3° photointerrupter
J8: Bottom LED
J9: Out of service LED
J10: Card slot solenoid
J11: First head
J12: .
J13: 8051 interface
JZ: Unpopulated connector
L1: LED
Q1: 4 MHz
R1, R24: 470
R2, R7, R27, R33: 47K
R3, R67: 330
R4: 22k
R5, R12, R28, R32, R45, R47: 220K
R6, R8, R15, R20, R26, R35, R46, R51, R66, R70: 4.7K
R9, R10, R25, R38, R52, R64: 10K
R11, R14, R37, R49, R50, R53, R54, R55, R56, R57, R58, R59, R60, R61, R62, R71: 100K
R13, R68: 1.0
R16, R17: 10k
R18: 6.8K
R19: 100
R21, R34: 5.6
R22, R23, R48: 2.2K
R29: 470
R30: 33k
R31: 4.7k
R36, R63: 1M
R39: 1k
R40: 1K
R41: 1.8K
R42: 0
R43: 22K
R44: 680
R65, R69: 150
R72: ?
RN1: R_Network08; R_Array_SIP9
T1, T2, T4, T6, T7, T8, T9, T10, T11, T12, T13, T14: BC817; SOT-23
T3: VN2406
T5: BC807; SOT-23
TP1, TP2: .
U1: HD6305Y2; QFP64
U2: 27C256; DIP-28_W15.24mm
U3: 74HC244
U4: PLCC44
U5: LM339
U6: LP2951-5.0_SOIC; SOIC-8_3.9x4.9mm_P1.27mm
U7, U8, U11, U12: "312"
U9: 40106
U10: "Y306"
U13, U14, U17: CD4052B
U16: LM324

Connections:
+5V: C1.2, C2.2, C3.2, C5.1, C9.1, C16.1, C20.1, C21.1, C22.1, C26.2, C31.1, J0.10, J1.10, J3.3, J3.8, R3.2, R4.1, R11.1, R16.2, R18.1, R42.1, R63.1, RN1.1 (common), T13.3 (C), T14.3 (C), U1.35 (~EA), U1.44 (VCC), U9.14 (VDD)
+BATT: J1.12, J1.13, J2.1, J3.5, J7.1, J12.1, J13.12, J13.13, R5.1, R12.1, R13.1, R21.1, R34.1, R68.1, R72.1
A13: J4.4, J6.2, U1.47 (A13), U2.26 (A13), U4.41
D0: AR1.2 (R1), U1.57 (D0), U2.11 (D0), U3.18 (1Y0)
D1: AR1.3 (R2), U1.56 (D1), U2.12 (D1), U3.16 (1Y1)
D2: AR1.4 (R3), U1.55 (D2), U2.13 (D2), U3.14 (1Y2)
D3: AR1.9 (R8), U1.54 (D3), U2.15 (D3), U3.12 (1Y3)
D4: AR1.8 (R7), U1.53 (D4), U2.16 (D4), U3.9 (2Y3)
D5: AR1.7 (R6), U1.52 (D5), U2.17 (D5), U3.7 (2Y2)
D6: AR1.6 (R5), U1.51 (D6), U2.18 (D6), U3.5 (2Y1)
D7: AR1.5 (R4), U1.50 (D7), U2.19 (D7), U3.3 (2Y0)
E: J13.9, JZ.31, U1.49 (E), U4.40
GND: C1.1, C3.1, C5.2, C9.2, C10.1, C16.2, C20.2, C21.2, C22.2, C26.1, C28.2, C31.2, D8.1 (K), J0.7, J1.1, J1.4, J1.7, J1.20, J4.1, J6.4, J7.4, R22.1, R30.2, R43.2, T1.2 (E), T3.1 (S), T12.2 (E), U1.22 (VSS), U1.58 (VSS), U9.7 (VSS), U10.1, U10.3
HEAD1-W1: I1.12, J11.1
HEAD1-W2: I1.11, J11.2
HEAD2-W1: D3.3 (A), D3.4 (A), I1.15, J1A.1
HEAD2-W2: D3.1 (K), I1.16, J1A.2, R69.2
HEAD3-W1: I1.13, I1.17, J6A.1
HEAD3-W2: I1.14, I1.18, J6A.2
J3-9: J3.9, R63.2, U4.17
unnamed: AR2.2 (R1), J2.3, R61.2
unnamed: AR2.3 (R2), J1.3, R62.2
unnamed: AR2.4 (R3), J7.3, R58.2
unnamed: AR2.5 (R4), J6.3, R71.2
unnamed: AR2.6 (R5), J4.2, R59.2
unnamed: AR2.7 (R6), J12.3, R60.1
unnamed: AR2.8 (R7), R57.2
unnamed: AR2.9 (R8), R56.2
unnamed: B1.2, D5.2 (A)
unnamed: B1.3, C7.2, C13.1, R13.2
unnamed: B1.5, D6.1 (A1), U10.7, U10.8
unnamed: B1.6, C14.2, C15.2
unnamed: C1.1, C6.1, R72.2, U6.8 (IN)
unnamed: C1.2, C6.2
unnamed: C2.1, J1.17, U1.10 (RST)
unnamed: C4.1, R2.2
unnamed: C4.2, J1A.3, J6A.3, J11.3, R2.1
unnamed: C10.2, L1.1 (K), R41.2, R46.2
unnamed: C11.1, C12.1
unnamed: C11.2, Q1.1, U1.62 (XTAL)
unnamed: C12.2, Q1.2, U1.63 (EXTAL)
unnamed: C7.1, C13.2
unnamed: C17.2, T4.2 (E)
unnamed: C18.1, C19.1, I1.3, TP1.1
unnamed: C18.2, C19.2, I1.6, TP2.1
unnamed: C23.1, D7.1 (K), R45.2, U9.3
unnamed: C23.2, U9.6
unnamed: C25.1, R36.1, T8.3 (C), U9.9
unnamed: C25.2, R23.2
unnamed: C26.1, U6.1 (OUT), U6.2 (SENSE)
unnamed: C26.2, U6.4 (GND)
unnamed: C27.1, D9.2 (A), R20.1
unnamed: C27.2, D9.1 (K), L1.2 (A), R35.2, T8.1 (B)
unnamed: C28.1, D8.2 (A), R19.2
unnamed: C29.1, C30.2, R25.2, R28.2, R32.2, U11.3, U12.3
unnamed: C29.2, R32.1, T11.3 (C), U12.2, U12.4
unnamed: C30.1, R28.1, T10.3 (C), U11.2, U11.4
unnamed: C32.1, R47.2
unnamed: C32.2, R48.1
unnamed: D1.1 (K), D1.2 (K), U4.34
unnamed: D3.2 (K), R65.1
unnamed: D7.2 (K), U9.11, U9.13
unnamed: D7.3 (A), D7.4 (A), U9.2
unnamed: D11.1 (K), J13.14
unnamed: I1.2, U1.27 (P2.3/A11)
unnamed: J0.19, U13.9 (B), U14.9 (B), U17.9 (B)
unnamed: J0.20, U13.10 (A), U14.10 (A), U17.10 (A)
unnamed: J1.1, J2.2
unnamed: J1.2, R67.1, U1.3 (P1.1/T2EX)
unnamed: J1.3, U1.2 (P1.0/T2)
unnamed: J1.5, R2.1
unnamed: J1.9, U1.21 (XTAL1)
unnamed: J1.16, R1.1
unnamed: J2.1, R2.2, R4.2
unnamed: J2.2, R1.2, R3.1
unnamed: J3.1, R18.2, T1.3 (C)
unnamed: J3.4, J3.7
unnamed: J3.10, R9.2
unnamed: J4.3, R29.1
unnamed: J5.1, U12.5, U12.6, U12.7, U12.8
unnamed: J5.2, U11.5, U11.6, U11.7, U11.8
unnamed: J6.1, J7.2
unnamed: J8.1, R24.1
unnamed: J9.1, R1.2
unnamed: J10.1, U7.5, U7.6, U7.7, U7.8
unnamed: J10.2, U8.5, U8.6, U8.7, U8.8
unnamed: J12.2, R3.2
unnamed: J13.1, J13.20, R49.2
unnamed: J13.10, R38.1, R52.1, R53.1, R54.1, R55.1
unnamed: R1.1, T14.2 (E)
unnamed: R4.1, R6.2, T7.1 (B)
unnamed: R4.2, T7.2 (E)
unnamed: R5.2, T7.3 (C), U7.2, U7.4
unnamed: R7.1, T6.2 (E)
unnamed: R7.2, R8.1, T6.1 (B)
unnamed: R9.1, R10.1, T2.1 (B)
unnamed: R10.2, T2.2 (E)
unnamed: R12.2, T6.3 (C), U8.2, U8.4
unnamed: R15.2, R33.1, T11.1 (B)
unnamed: R16.1, R17.1, T1.1 (B)
unnamed: R19.1, R20.2, T9.1 (B), U11.1, U12.1
unnamed: R21.2, R68.2, U8.3
unnamed: R22.2, T9.2 (E)
unnamed: R23.1, R45.1, U9.4, U9.5
unnamed: R24.2, T13.2 (E)
unnamed: R26.2, R27.1, T10.1 (B)
unnamed: R27.2, T10.2 (E)
unnamed: R3.1, R29.2, R67.2, T12.3 (C)
unnamed: R30.1, R31.1, T12.1 (B)
unnamed: R33.2, T11.2 (E)
unnamed: R34.2, U7.3
unnamed: R35.1, T8.2 (E)
unnamed: R39.1, U10.2
unnamed: R39.2, U9.10, U9.12
unnamed: R40.1, U10.4
unnamed: R41.1, R44.2, T3.3 (D)
unnamed: R43.1, R44.1, U10.5, U10.6
unnamed: R48.2, U9.8
unnamed: R50.1, U2.27 (A14)
unnamed: R50.2, R51.2, U2.14 (GND)
unnamed: R51.1, U2.22 (~OE)
unnamed: R56.1, U3.17 (2A0)
unnamed: R57.1, U3.15 (2A1)
unnamed: R58.1, U3.6 (1A2)
unnamed: R59.1, U3.11 (2A3)
unnamed: R60.2, U3.13 (2A2)
unnamed: R61.1, U3.2 (1A0)
unnamed: R62.1, U3.4 (1A1)
unnamed: R64.1, T5.2 (E)
unnamed: R64.2, R66.1, T5.1 (B)
unnamed: R65.2, R66.2, T4.3 (C)
unnamed: R69.1, T5.3 (C)
unnamed: R70.2, T4.1 (B)
unnamed: R71.1, U3.8 (1A3)
unnamed: RN1.2 (R1), U1.43 (P0.0/AD0)
unnamed: RN1.3 (R2), U1.42 (P0.1/AD1)
unnamed: RN1.4 (R3), U1.41 (P0.2/AD2)
unnamed: RN1.5 (R4), U1.40 (P0.3/AD3)
unnamed: RN1.6 (R5), U1.39 (P0.4/AD4)
unnamed: RN1.7 (R6), U1.38 (P0.5/AD5)
unnamed: RN1.8 (R7), U1.37 (P0.6/AD6)
unnamed: RN1.9 (R8), U1.36 (P0.7/AD7)
unnamed: U1.34 (NIC_4), U2.10 (A0), U4.12
unnamed: U1.35 (~EA), U2.9 (A1), U4.11
unnamed: U1.36 (P0.7/AD7), U2.8 (K), U4.10
unnamed: U1.37 (P0.6/AD6), U2.7 (A3), U4.9
unnamed: U1.38 (P0.5/AD5), U2.6 (A4), U4.8
unnamed: U1.39 (P0.4/AD4), U2.5 (FB), U4.5
unnamed: U1.40 (P0.3/AD3), U2.4 (A), U4.4
unnamed: U1.41 (P0.2/AD2), U2.3 (A7), U4.3
unnamed: U1.42 (P0.1/AD1), U2.25 (A8), U4.2
unnamed: U1.43 (P0.0/AD0), U2.24 (A9), U4.1
unnamed: U1.44 (VCC), U2.21 (A10), U4.44
unnamed: U1.45 (A11), U2.23 (A11), U4.43
unnamed: U1.46 (A12), U2.2 (A12), U4.42
unnamed: U2.20 (~CE), U4.38
unnamed: U3.1 (1OE), U3.19 (2OE), U4.37
unnamed: U4.7, U4.13, U4.14, U4.15, U4.16, U4.18
unnamed: U4.19, U4.20, U4.21, U4.22
unnamed: U6.6 (VTAP), U6.7 (FEEDBACK)
PA0: JZ.34, R26.1, U1.9 (P1.7/CEX4)
PA1: JZ.21, R15.1, U1.8 (P1.6/CEX3)
PA2: JZ.33, R40.2, U1.7 (P1.5/CEX2)
PA3: J13.2, JZ.5, R52.2, U1.6 (P1.4/CEX1)
PA4: J13.3, JZ.27, R38.2, U1.5 (P1.3/CEX0)
PA5: JZ.30, R70.1, U1.4 (P1.2/ECI)
PA6: I1.8, JZ.29, U1.3 (P1.1/T2EX)
PA7: I1.9, JZ.22, U1.2 (P1.0/T2)
PB0: I1.4, JZ.13, U1.17 (P3.5/T1)
PB1: I1.20, JZ.16, U1.16 (P3.4/T0)
PB2: I1.19, JZ.35, U1.15 (P3.3/~INT1)
PB3: JZ.17, R31.2, U1.14 (P3.2/~INT0)
PB4: JZ.28, T14.1 (B), U1.13 (P3.1/TXD)
PB5: JZ.26, T13.1 (B), U1.12 (NIC_2)
PB6: JZ.32, R6.1, U1.11 (P3.0/RXD)
PB7: JZ.24, R8.2, U1.10 (RST)
PC0: J13.11, JZ.3, T3.2 (G), U1.25 (P2.1/A9)
PC1: J13.4, JZ.20, U1.24 (P2.0/A8)
PC2: J13.6, JZ.11, U1.23 (NIC_3)
PC3: J13.16, JZ.9, U1.22 (VSS)
PC4: J13.5, JZ.12, U1.21 (XTAL1)
PC5: J13.17, JZ.10, U1.20 (XTAL2)
PC6: J13.15, JZ.15, R37.2, U1.19 (P3.7/~RD), U9.1
PC7: JZ.36, R17.2, U1.18 (P3.6/~WR)
PD1: JZ.2
PD2: I1.1, JZ.4, U1.28 (P2.4/A12)
PD3: I1.5, JZ.1, U1.29 (P2.5/A13)
PD4: J13.7, JZ.18, R54.2, U1.30 (P2.6/A14)
PD5: J13.18, JZ.8, R53.2, U1.31 (P2.7/A15)
PD6: JZ.7, R11.2, T2.3 (C), U1.32 (~PSEN)
PD7: J13.8, JZ.14, R55.2, U1.33 (ALE/~PROG)
R/~W: JZ.25, U1.48 (R/~W), U4.36
TIMER: J13.19, R49.1, U1.1 (NIC_1)
VDC: C14.1, C15.1, D5.1 (K), D11.2 (A), R25.1, R46.1, T9.3 (C)
~RST: C8.1, D1.3 (A), D1.4 (A), JZ.23, R14.1, U1.59 (~RST)
~STBY: JZ.19, R42.2, U1.61 (~STBY)

Notes on the sheet:
Analog head interface ceramic module. No designators present on module. All reported values for components are direct measurements. Resistors are thick-film on ceramic, laser trimmed.
Main LIOD PCB IPM EM105 16-1993 Note: SMD resistor and caps have no designators on the silkscreen. Designators are however correct for through hole parts.
